leomanes/stargate/BOM/stargate_2.1.2.jpg

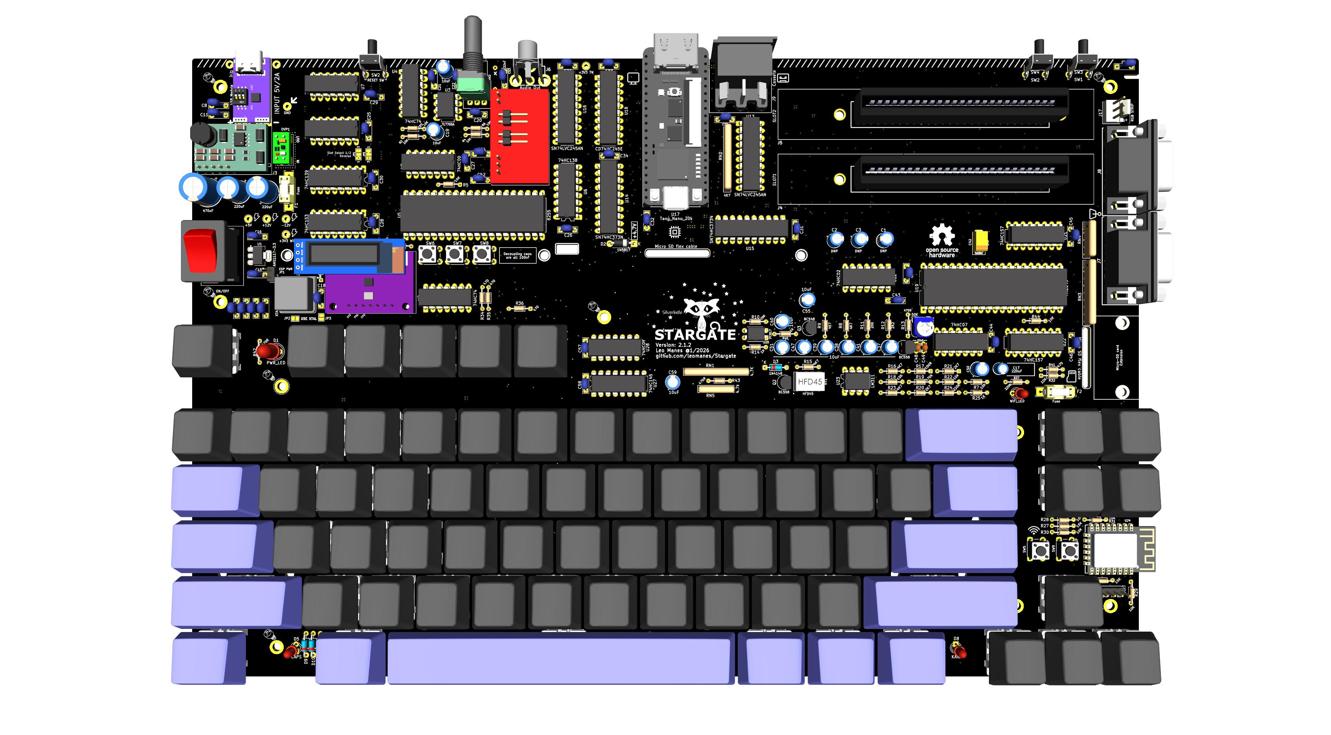
BOM/stargate_2.1.2.jpg
