leomanes/stargate/build/imgs/image009.png

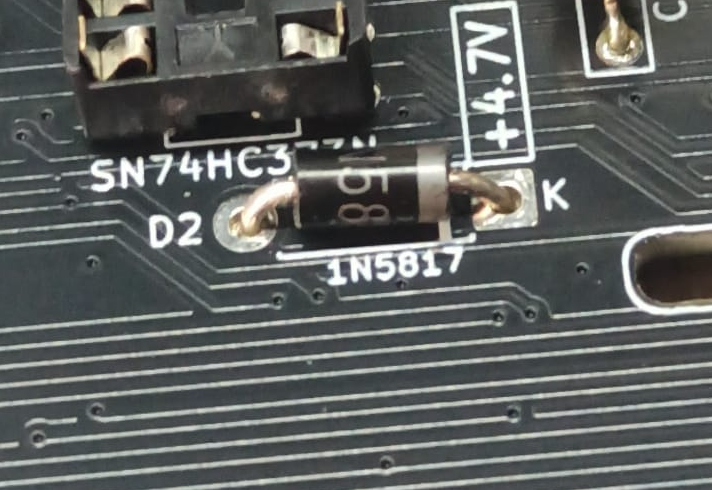
build/imgs/image009.png
