leomanes/stargate/kicad/version v2.1.3 production/Keyboard.kicad_sch

## KiCad design kicad/version v2.1.3 production/Keyboard.kicad_sch (2026-06-13)

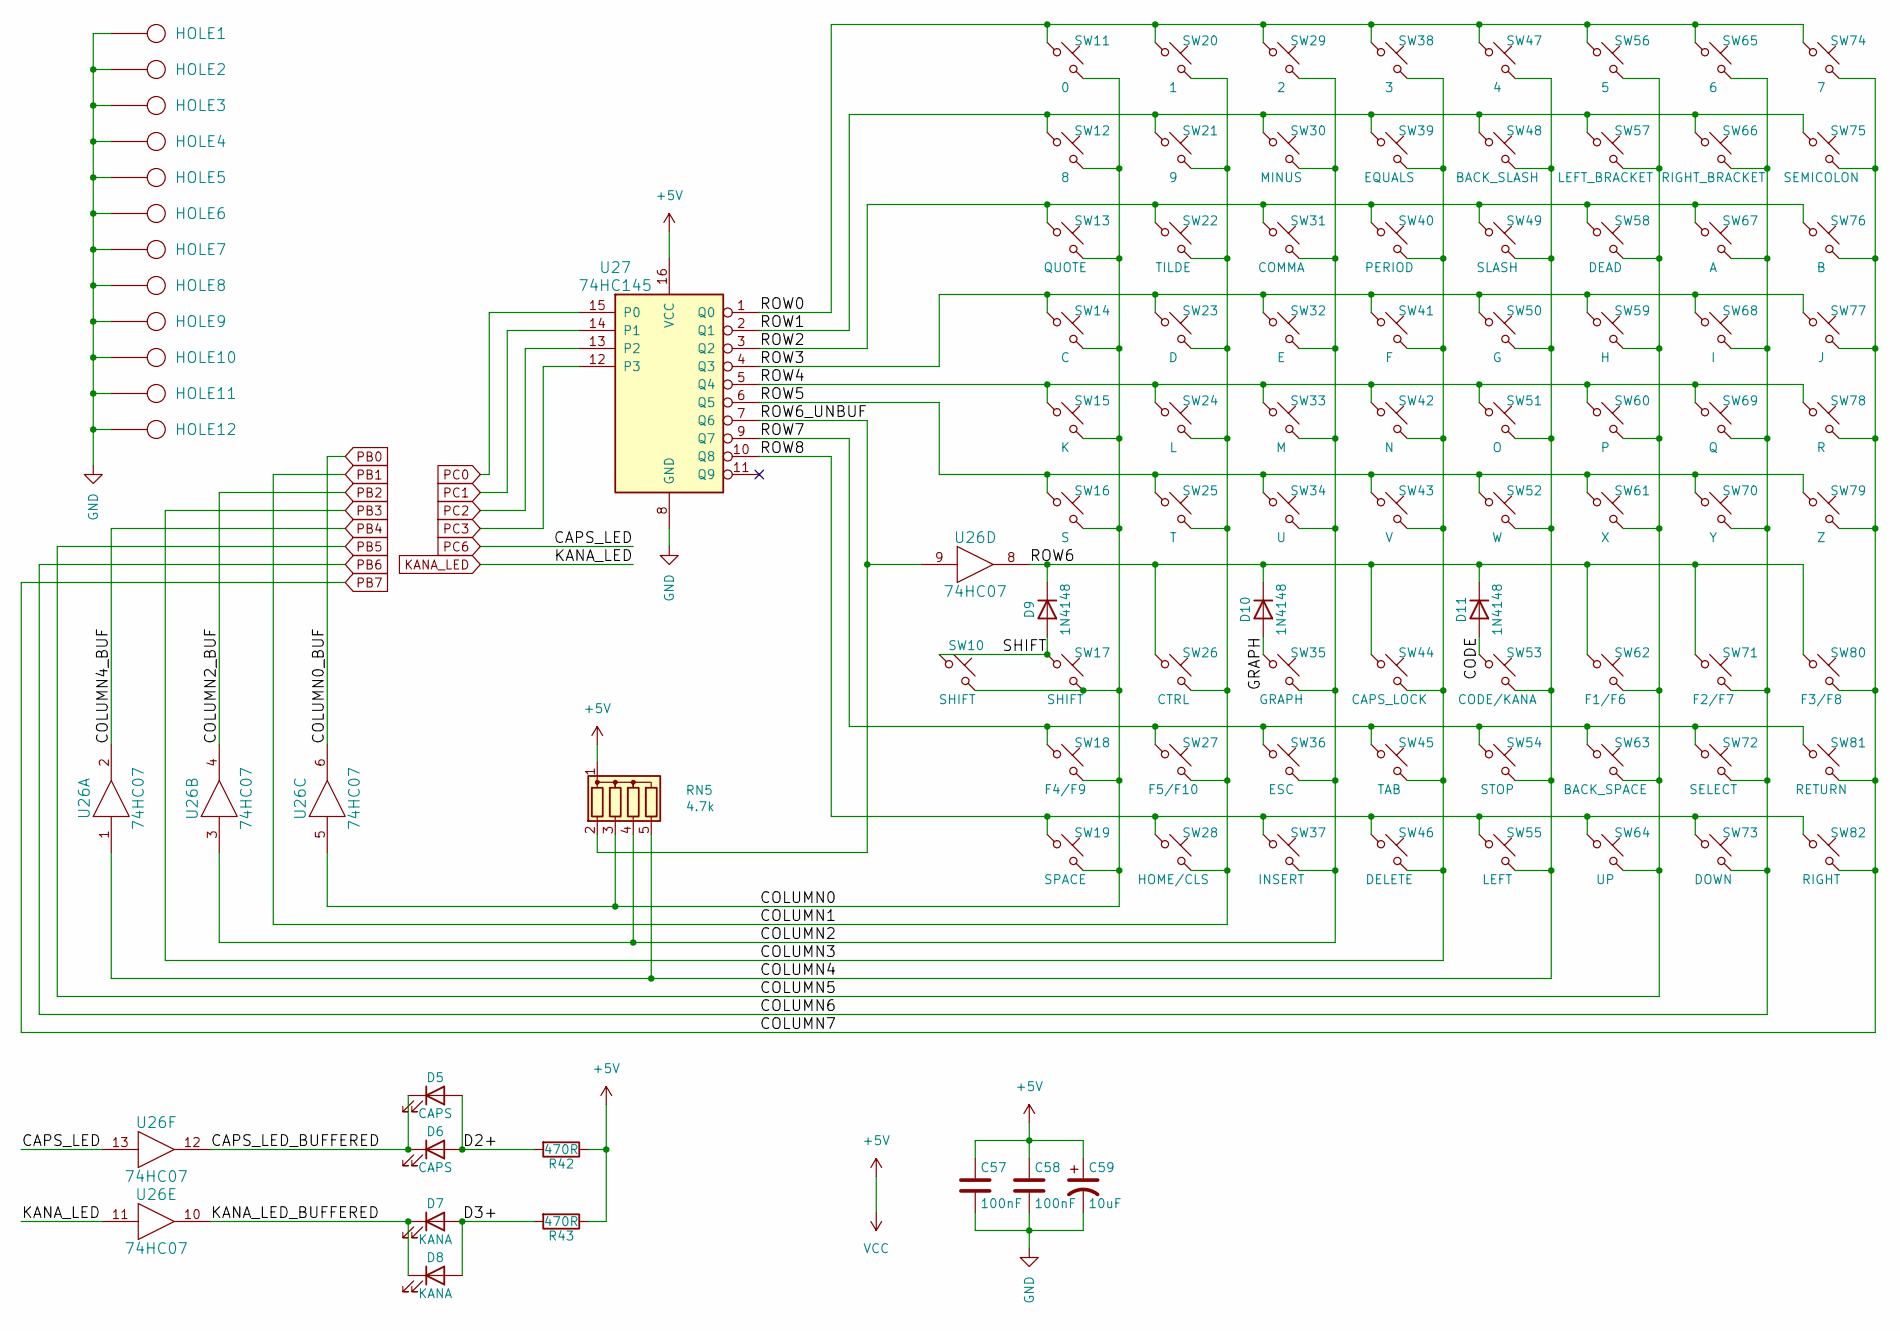
[picture p44: schematic Keyboard.kicad_sch]

Parts:
C57, C58: 100nF; CP_P5.00mm
C59: 10uF; CP_Radial_D5.0mm_P2.50mm
D5, D6: CAPS; LED_D3.0mm
D7, D8: KANA; LED_D3.0mm
D9, D10, D11: 1N4148; D_DO-35_SOD27_P7.62mm_Horizontal
HOLE1, HOLE2, HOLE3, HOLE4, HOLE5, HOLE6, HOLE7, HOLE8, HOLE9, HOLE12: HOLE; MountingHole_3mm_Pad_TopBottom_new
HOLE10, HOLE11: HOLE; MountingHole_2mm_Pad_TopBottom_new
R42, R43: 470R; R_Axial_DIN0204_L3.6mm_D1.6mm_P7.62mm_Horizontal
RN5: 4.7k; R_Array_SIP5
SW10: SHIFT; CHERRY_PCB_275H
SW11: 0; CHERRY_PCB_100H
SW12: 8; CHERRY_PCB_100H
SW13: QUOTE; CHERRY_PCB_100H
SW14: C; CHERRY_PCB_100H
SW15: K; CHERRY_PCB_100H
SW16: S; CHERRY_PCB_100H
SW17: SHIFT; CHERRY_PCB_225H
SW18: F4/F9; CHERRY_PCB_100H
SW19: SPACE; CHERRY_PCB_625H
SW20: 1; CHERRY_PCB_100H
SW21: 9; CHERRY_PCB_100H
SW22: TILDE; CHERRY_PCB_100H
SW23: D; CHERRY_PCB_100H
SW24: L; CHERRY_PCB_100H
SW25: T; CHERRY_PCB_100H
SW26: CTRL; CHERRY_PCB_125H
SW27: F5/F10; CHERRY_PCB_100H
SW28: HOME/CLS; CHERRY_PCB_100H
SW29: 2; CHERRY_PCB_100H
SW30: MINUS; CHERRY_PCB_100H
SW31: COMMA; CHERRY_PCB_100H
SW32: E; CHERRY_PCB_100H
SW33: M; CHERRY_PCB_100H
SW34: U; CHERRY_PCB_100H
SW35: GRAPH; CHERRY_PCB_125H
SW36: ESC; CHERRY_PCB_100H
SW37: INSERT; CHERRY_PCB_100H
SW38: 3; CHERRY_PCB_100H
SW39: EQUALS; CHERRY_PCB_100H
SW40: PERIOD; CHERRY_PCB_100H
SW41: F; CHERRY_PCB_100H
SW42: N; CHERRY_PCB_100H
SW43: V; CHERRY_PCB_100H
SW44: CAPS_LOCK; CHERRY_PCB_175H
SW45: TAB; CHERRY_PCB_150H
SW46: DELETE; CHERRY_PCB_100H
SW47: 4; CHERRY_PCB_100H
SW48: BACK_SLASH; CHERRY_PCB_150H
SW49: SLASH; CHERRY_PCB_100H
SW50: G; CHERRY_PCB_100H
SW51: O; CHERRY_PCB_100H
SW52: W; CHERRY_PCB_100H
SW53: CODE/KANA; CHERRY_PCB_125H
SW54: STOP; CHERRY_PCB_100H
SW55: LEFT; CHERRY_PCB_100H
SW56: 5; CHERRY_PCB_100H
SW57: LEFT_BRACKET; CHERRY_PCB_100H
SW58: DEAD; CHERRY_PCB_125H
SW59: H; CHERRY_PCB_100H
SW60: P; CHERRY_PCB_100H
SW61: X; CHERRY_PCB_100H
SW62: F1/F6; CHERRY_PCB_100H
SW63: BACK_SPACE; CHERRY_PCB_200H
SW64: UP; CHERRY_PCB_100H
SW65: 6; CHERRY_PCB_100H
SW66: RIGHT_BRACKET; CHERRY_PCB_100H
SW67: A; CHERRY_PCB_100H
SW68: I; CHERRY_PCB_100H
SW69: Q; CHERRY_PCB_100H
SW70: Y; CHERRY_PCB_100H
SW71: F2/F7; CHERRY_PCB_100H
SW72: SELECT; CHERRY_PCB_125H
SW73: DOWN; CHERRY_PCB_100H
SW74: 7; CHERRY_PCB_100H
SW75: SEMICOLON; CHERRY_PCB_100H
SW76: B; CHERRY_PCB_100H
SW77: J; CHERRY_PCB_100H
SW78: R; CHERRY_PCB_100H
SW79: Z; CHERRY_PCB_100H
SW80: F3/F8; CHERRY_PCB_100H
SW81: RETURN; CHERRY_PCB_225H
SW82: RIGHT; CHERRY_PCB_100H
U26: 74HC07; DIP-14_W7.62mm
U27: 74HC145; DIP-16_W7.62mm

Connections:
+5V: C57.1, C58.1, C59.1, R42.1, R43.1, RN5.1 (common), U27.16 (VCC)
CAPS_LED_BUFFERED: D5.1 (K), D6.1 (K), U26.12
CODE: D11.2 (A), SW53.1
COLUMN0: RN5.3 (R2), SW10.2, SW11.2, SW12.2, SW13.2, SW14.2, SW15.2, SW16.2, SW17.2, SW18.2, SW19.2, U26.5
COLUMN2: RN5.4 (R3), SW29.2, SW30.2, SW31.2, SW32.2, SW33.2, SW34.2, SW35.2, SW36.2, SW37.2, U26.3
COLUMN4: RN5.5 (R4), SW47.2, SW48.2, SW49.2, SW50.2, SW51.2, SW52.2, SW53.2, SW54.2, SW55.2, U26.1
D2+: D5.2 (A), D6.2 (A), R42.2
D3+: D7.2 (A), D8.2 (A), R43.2
GND: C57.2, C58.2, C59.2, HOLE1.1, HOLE2.1, HOLE3.1, HOLE4.1, HOLE5.1, HOLE6.1, HOLE7.1, HOLE8.1, HOLE9.1, HOLE10.1, HOLE11.1, HOLE12.1, U27.8 (GND)
GRAPH: D10.2 (A), SW35.1
KANA_LED: U26.11
KANA_LED_BUFFERED: D7.1 (K), D8.1 (K), U26.10
PB0: U26.6
PB1: SW20.2, SW21.2, SW22.2, SW23.2, SW24.2, SW25.2, SW26.2, SW27.2, SW28.2
PB2: U26.4
PB3: SW38.2, SW39.2, SW40.2, SW41.2, SW42.2, SW43.2, SW44.2, SW45.2, SW46.2
PB4: U26.2
PB5: SW56.2, SW57.2, SW58.2, SW59.2, SW60.2, SW61.2, SW62.2, SW63.2, SW64.2
PB6: SW65.2, SW66.2, SW67.2, SW68.2, SW69.2, SW70.2, SW71.2, SW72.2, SW73.2
PB7: SW74.2, SW75.2, SW76.2, SW77.2, SW78.2, SW79.2, SW80.2, SW81.2, SW82.2
PC0: U27.15 (P0)
PC1: U27.14 (P1)
PC2: U27.13 (P2)
PC3: U27.12 (P3)
PC6: U26.13
ROW0: SW11.1, SW20.1, SW29.1, SW38.1, SW47.1, SW56.1, SW65.1, SW74.1, U27.1 (Q0)
ROW1: SW12.1, SW21.1, SW30.1, SW39.1, SW48.1, SW57.1, SW66.1, SW75.1, U27.2 (Q1)
ROW2: SW13.1, SW22.1, SW31.1, SW40.1, SW49.1, SW58.1, SW67.1, SW76.1, U27.3 (Q2)
ROW3: SW14.1, SW23.1, SW32.1, SW41.1, SW50.1, SW59.1, SW68.1, SW77.1, U27.4 (Q3)
ROW4: SW15.1, SW24.1, SW33.1, SW42.1, SW51.1, SW60.1, SW69.1, SW78.1, U27.5 (Q4)
ROW5: SW16.1, SW25.1, SW34.1, SW43.1, SW52.1, SW61.1, SW70.1, SW79.1, U27.6 (Q5)
ROW6: D9.1 (K), D10.1 (K), D11.1 (K), SW26.1, SW44.1, SW62.1, SW71.1, SW80.1, U26.8
ROW6_UNBUF: RN5.2 (R1), U26.9, U27.7 (Q6)
ROW7: SW18.1, SW27.1, SW36.1, SW45.1, SW54.1, SW63.1, SW72.1, SW81.1, U27.9 (Q7)
ROW8: SW19.1, SW28.1, SW37.1, SW46.1, SW55.1, SW64.1, SW73.1, SW82.1, U27.10 (Q8)
SHIFT: D9.2 (A), SW10.1, SW17.1
