leomanes/stargate/kicad/version v2.1.3 production/RGBstrip.kicad_sch

## KiCad design kicad/version v2.1.3 production/RGBstrip.kicad_sch (2026-06-13)

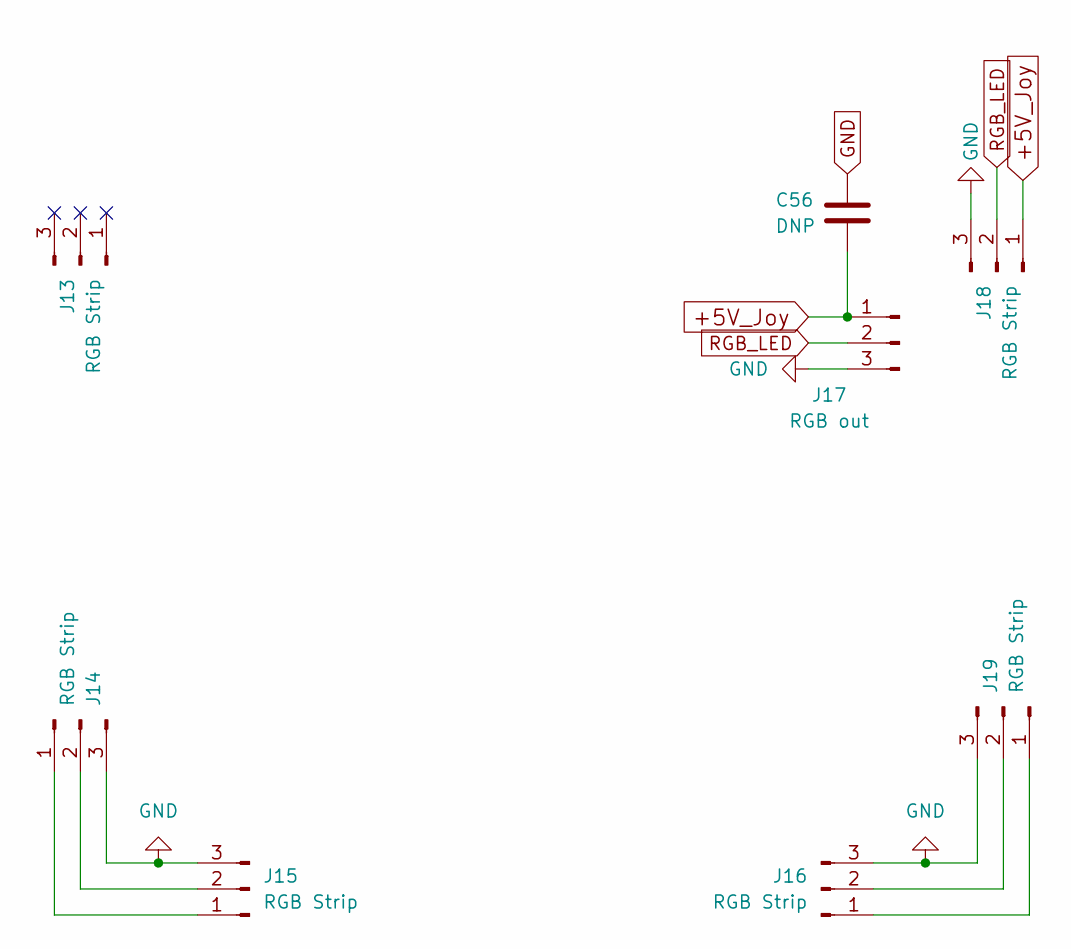
[picture p45: schematic RGBstrip.kicad_sch]

Parts:
C56: DNP; CP_P5.00mm; LCSC C14663
J13, J15, J19: RGB Strip; ledstrip_end
J14, J16, J18: RGB Strip; ledstrip
J17: RGB out; FanPinHeader_1x03_P2.54mm_Vertical

Connections:
+5V_Joy: C56.1, J17.1, J18.1
GND: C56.2, J14.3, J15.3, J16.3, J17.3, J18.3, J19.3
unnamed: J14.1, J15.1
unnamed: J14.2, J15.2
unnamed: J16.1, J19.1
unnamed: J16.2, J19.2
RGB_LED: J17.2, J18.2
