leomanes/stargate/kicad/version v2.1.3 production/amplifier.kicad_sch

## KiCad design kicad/version v2.1.3 production/amplifier.kicad_sch (2026-06-13)

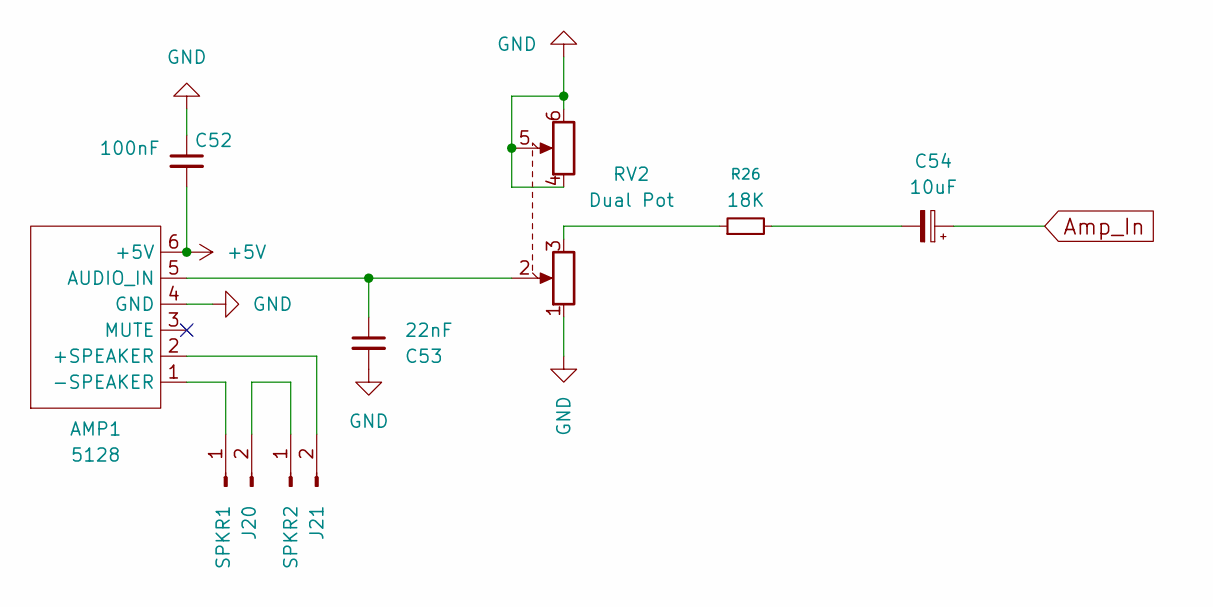
[picture p46: schematic amplifier.kicad_sch]

Parts:
AMP1: 5128; Amp5128
C52: 100nF; CP_P5.00mm
C53: 22nF; CP_P5.00mm
C54: 10uF; CP_Radial_D5.0mm_P2.50mm
J20: SPKR1; PinHeader_1x02_P2.54mm_Vertical
J21: SPKR2; PinHeader_1x02_P2.54mm_Vertical
R26: 18K; R_Axial_DIN0204_L3.6mm_D1.6mm_P7.62mm_Horizontal
RV2: Dual Pot; Potentiometer_Alps_RK097_Dual_Horizontal

Connections:
+5V: AMP1.6 (+5V), C52.2
Amp_In: C54.1
GND: AMP1.4 (GND), C52.1, C53.2, RV2.1, RV2.4, RV2.5, RV2.6
unnamed: AMP1.1 (-SPEAKER), J20.1
unnamed: AMP1.2 (+SPEAKER), J21.2
unnamed: AMP1.5 (AUDIO_IN), C53.1, RV2.2
unnamed: C54.2, R26.2
unnamed: J20.2, J21.1
unnamed: R26.1, RV2.3
