leomanes/stargate/kicad/version v2.1.3 production/bluetooth.kicad_sch

## KiCad design kicad/version v2.1.3 production/bluetooth.kicad_sch (2026-06-13)

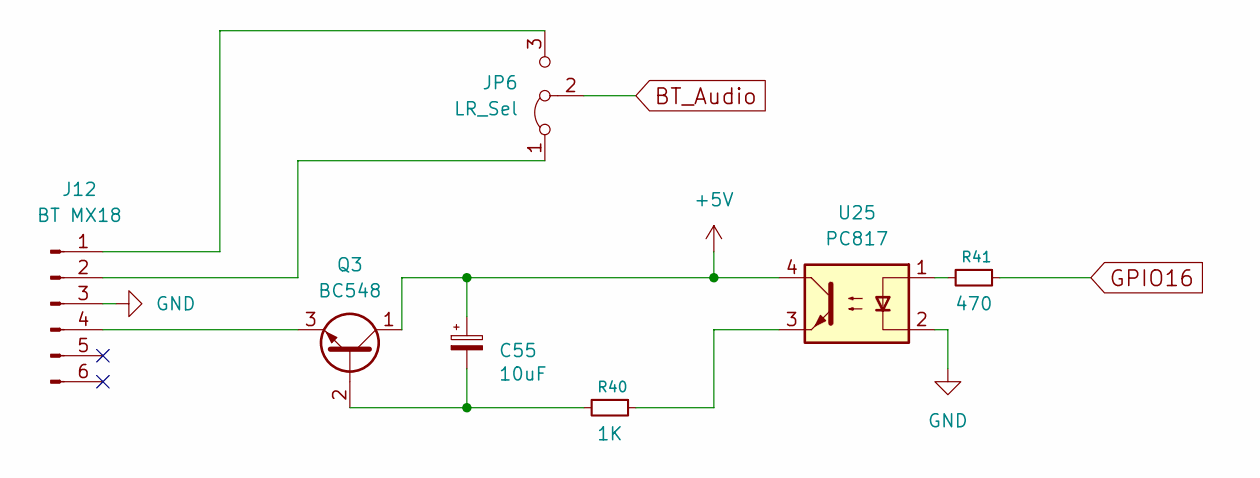
[picture p47: schematic bluetooth.kicad_sch]

Parts:
C55: 10uF; CP_Radial_D5.0mm_P2.50mm
J12: BT MX18; MH-M18
JP6: LR_Sel; SolderJumper-3_P1.3mm_Bridged12_Pad1.0x1.5mm_NumberLabels
Q3: BC548; TO-92
R40: 1K; R_Axial_DIN0204_L3.6mm_D1.6mm_P7.62mm_Horizontal
R41: 470; R_Axial_DIN0204_L3.6mm_D1.6mm_P7.62mm_Horizontal
U25: PC817; DIP-4_W7.62mm

Connections:
+5V: C55.1, Q3.1 (C), U25.4
BT_Audio: JP6.2 (C)
GND: J12.3, U25.2
GPIO16: R41.1
unnamed: C55.2, Q3.2 (B), R40.2
unnamed: J12.1, JP6.3 (B)
unnamed: J12.2, JP6.1 (A)
unnamed: J12.4, Q3.3 (E)
unnamed: R40.1, U25.3
unnamed: R41.2, U25.1
