leomanes/stargate/kicad/version v2.1.3 production/casette.kicad_sch

## KiCad design kicad/version v2.1.3 production/casette.kicad_sch (2026-06-13)

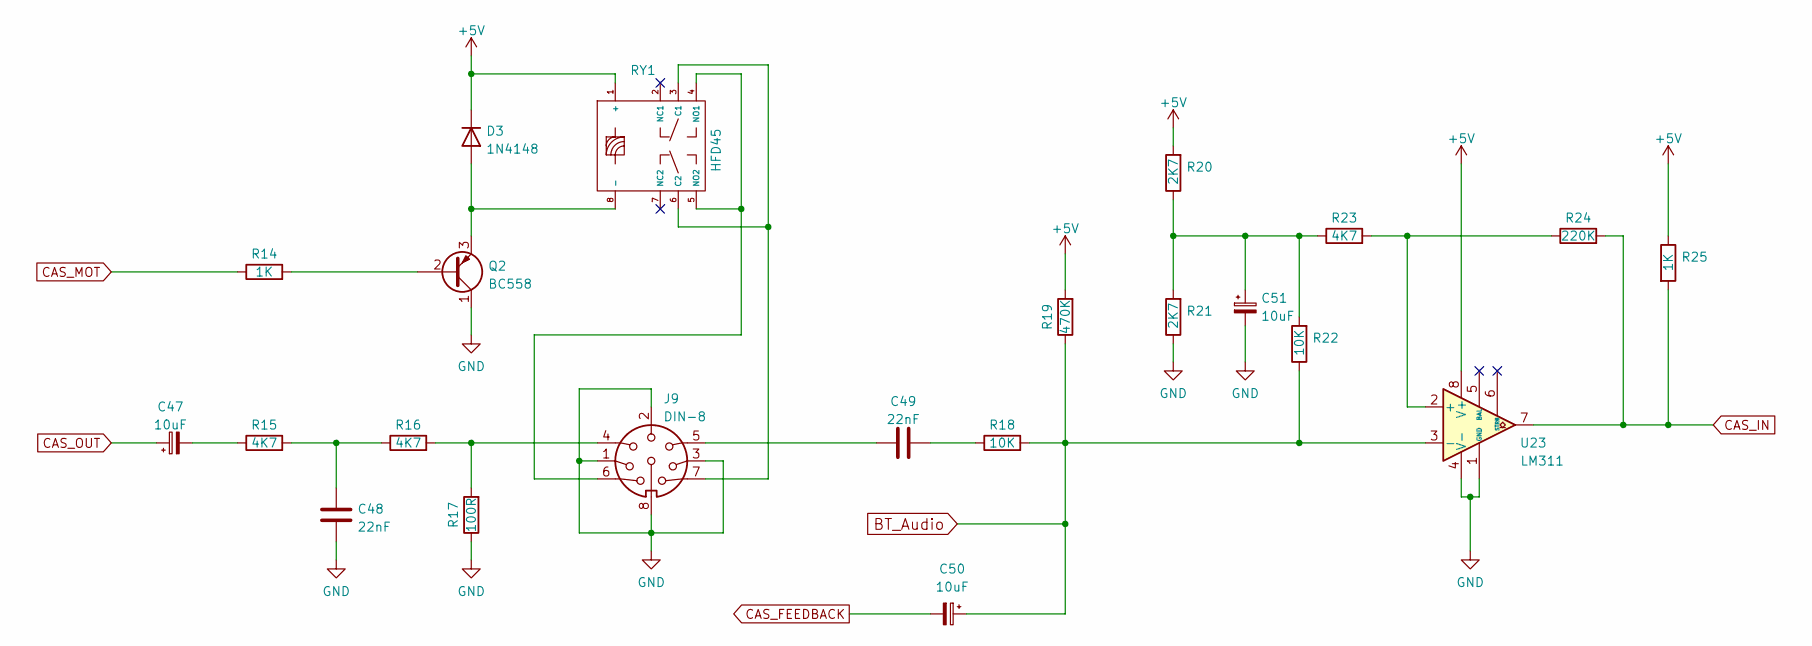
[picture p48: schematic casette.kicad_sch]

Parts:
C47, C50, C51: 10uF; CP_Radial_D5.0mm_P2.50mm
C48, C49: 22nF; C_Disc_D3.0mm_W2.0mm_P2.50mm
D3: 1N4148; D_DO-35_SOD27_P7.62mm_Horizontal
J9: DIN-8; DIN8
Q2: BC558; TO-92
R14, R25: 1K; R_Axial_DIN0204_L3.6mm_D1.6mm_P7.62mm_Horizontal
R15, R16, R23: 4K7; R_Axial_DIN0204_L3.6mm_D1.6mm_P7.62mm_Horizontal
R17: 100R; R_Axial_DIN0204_L3.6mm_D1.6mm_P7.62mm_Horizontal
R18, R22: 10K; R_Axial_DIN0204_L3.6mm_D1.6mm_P7.62mm_Horizontal
R19: 470K; R_Axial_DIN0204_L3.6mm_D1.6mm_P7.62mm_Horizontal
R20, R21: 2K7; R_Axial_DIN0204_L3.6mm_D1.6mm_P7.62mm_Horizontal
R24: 220K; R_Axial_DIN0204_L3.6mm_D1.6mm_P7.62mm_Horizontal
RY1: HFD45
U23: LM311; DIP-8_W7.62mm_LongPads

Connections:
+5V: D3.1 (K), R19.2, R20.2, R25.1, RY1.1 (+), U23.8 (V+)
BT_Audio: C50.1, R18.2, R19.1, R22.1, U23.3 (-)
CAS_FEEDBACK: C50.2
CAS_IN: R24.2, R25.2, U23.7
CAS_MOT: R14.1
CAS_OUT: C47.1
GND: C48.1, C51.2, J9.1, J9.2, J9.3, J9.8, Q2.1 (C), R17.1, R21.1, U23.1 (GND), U23.4 (V-)
unnamed: C47.2, R15.1
unnamed: C48.2, R15.2, R16.1
unnamed: C49.1, J9.5
unnamed: C49.2, R18.1
unnamed: C51.1, R20.1, R21.2, R22.2, R23.1
unnamed: D3.2 (A), Q2.3 (E), RY1.8 (-)
unnamed: J9.4, R16.2, R17.2
unnamed: J9.6, RY1.4 (NO1), RY1.5 (NO2)
unnamed: J9.7, RY1.3 (C1), RY1.6 (C2)
unnamed: Q2.2 (B), R14.2
unnamed: R23.2, R24.1, U23.2 (+)
