leomanes/stargate/kicad/version v2.1.3 production/clock.kicad_sch

## KiCad design kicad/version v2.1.3 production/clock.kicad_sch (2026-06-13)

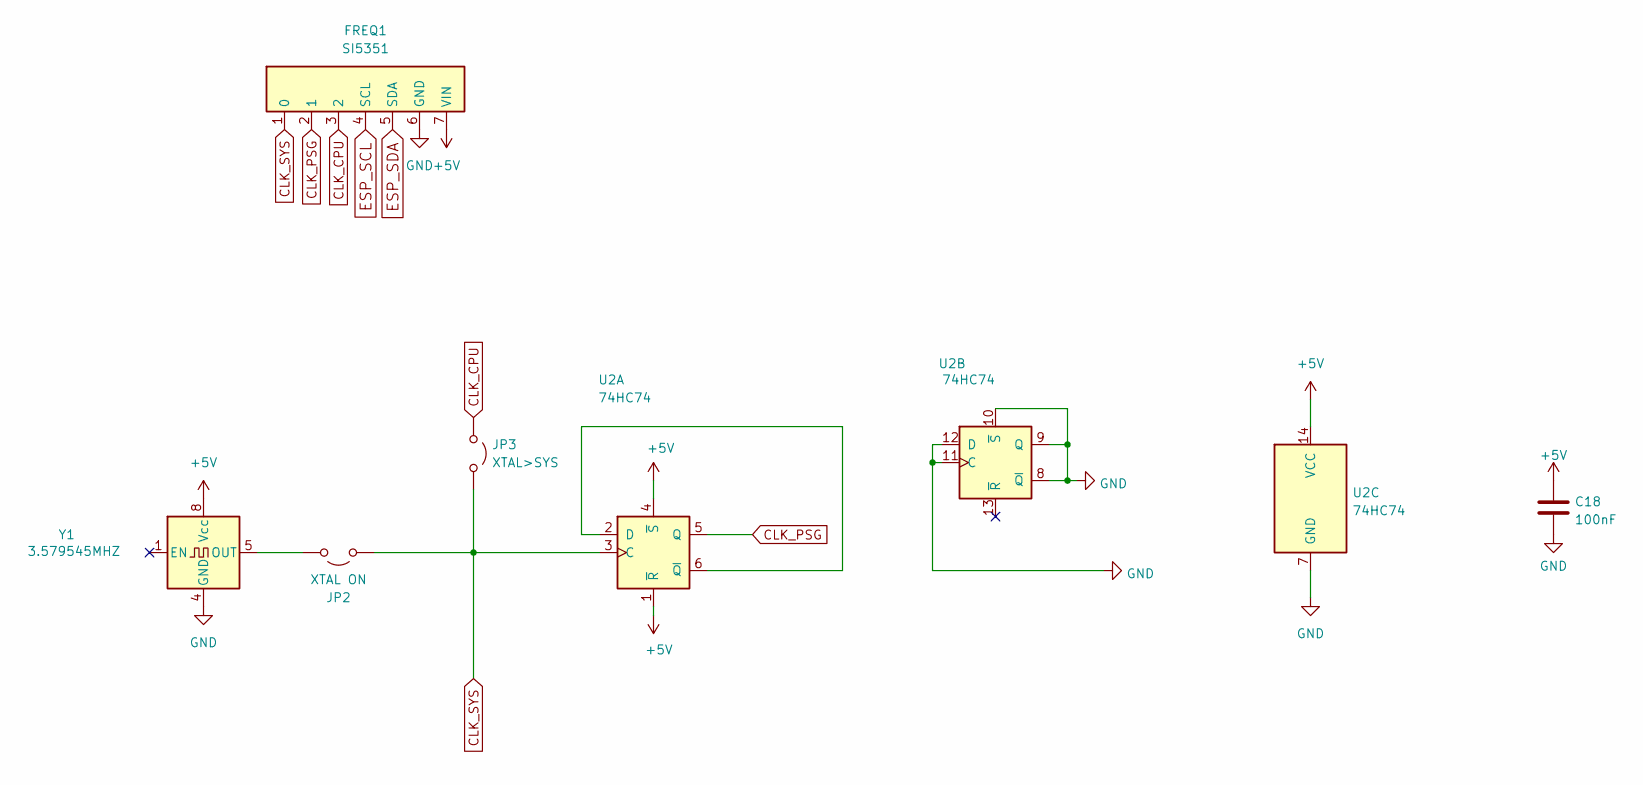
[picture p49: schematic clock.kicad_sch]

Parts:
C18: 100nF; CP_P5.00mm
FREQ1: SI5351; si5351
JP2: XTAL ON; SolderJumper-2_P1.3mm_Open_Pad1.0x1.5mm
JP3: XTAL>SYS; SolderJumper-2_P1.3mm_Open_Pad1.0x1.5mm
U2: 74HC74; DIP-14_W7.62mm_LongPads
Y1: 3.579545MHZ; Oscillator_DIP-8

Connections:
+5V: C18.1, FREQ1.7 (VIN), U2.1 (~R), U2.4 (~S), U2.14 (VCC), Y1.8 (Vcc)
CLK_CPU: FREQ1.3 (2), JP3.1 (A)
CLK_PSG: FREQ1.2 (1), U2.5 (Q)
CLK_SYS: FREQ1.1 (0), JP2.2 (B), JP3.2 (B), U2.3 (C)
ESP_SCL: FREQ1.4 (SCL)
ESP_SDA: FREQ1.5 (SDA)
GND: C18.2, FREQ1.6 (GND), U2.7 (GND), U2.8 (~Q), U2.9 (Q), U2.10 (~S), U2.11 (C), U2.12 (D), Y1.4 (GND)
unnamed: JP2.1 (A), Y1.5 (OUT)
unnamed: U2.2 (D), U2.6 (~Q)
