leomanes/stargate/kicad/version v2.1.3 production/cpu.kicad_sch

## KiCad design kicad/version v2.1.3 production/cpu.kicad_sch (2026-06-13)

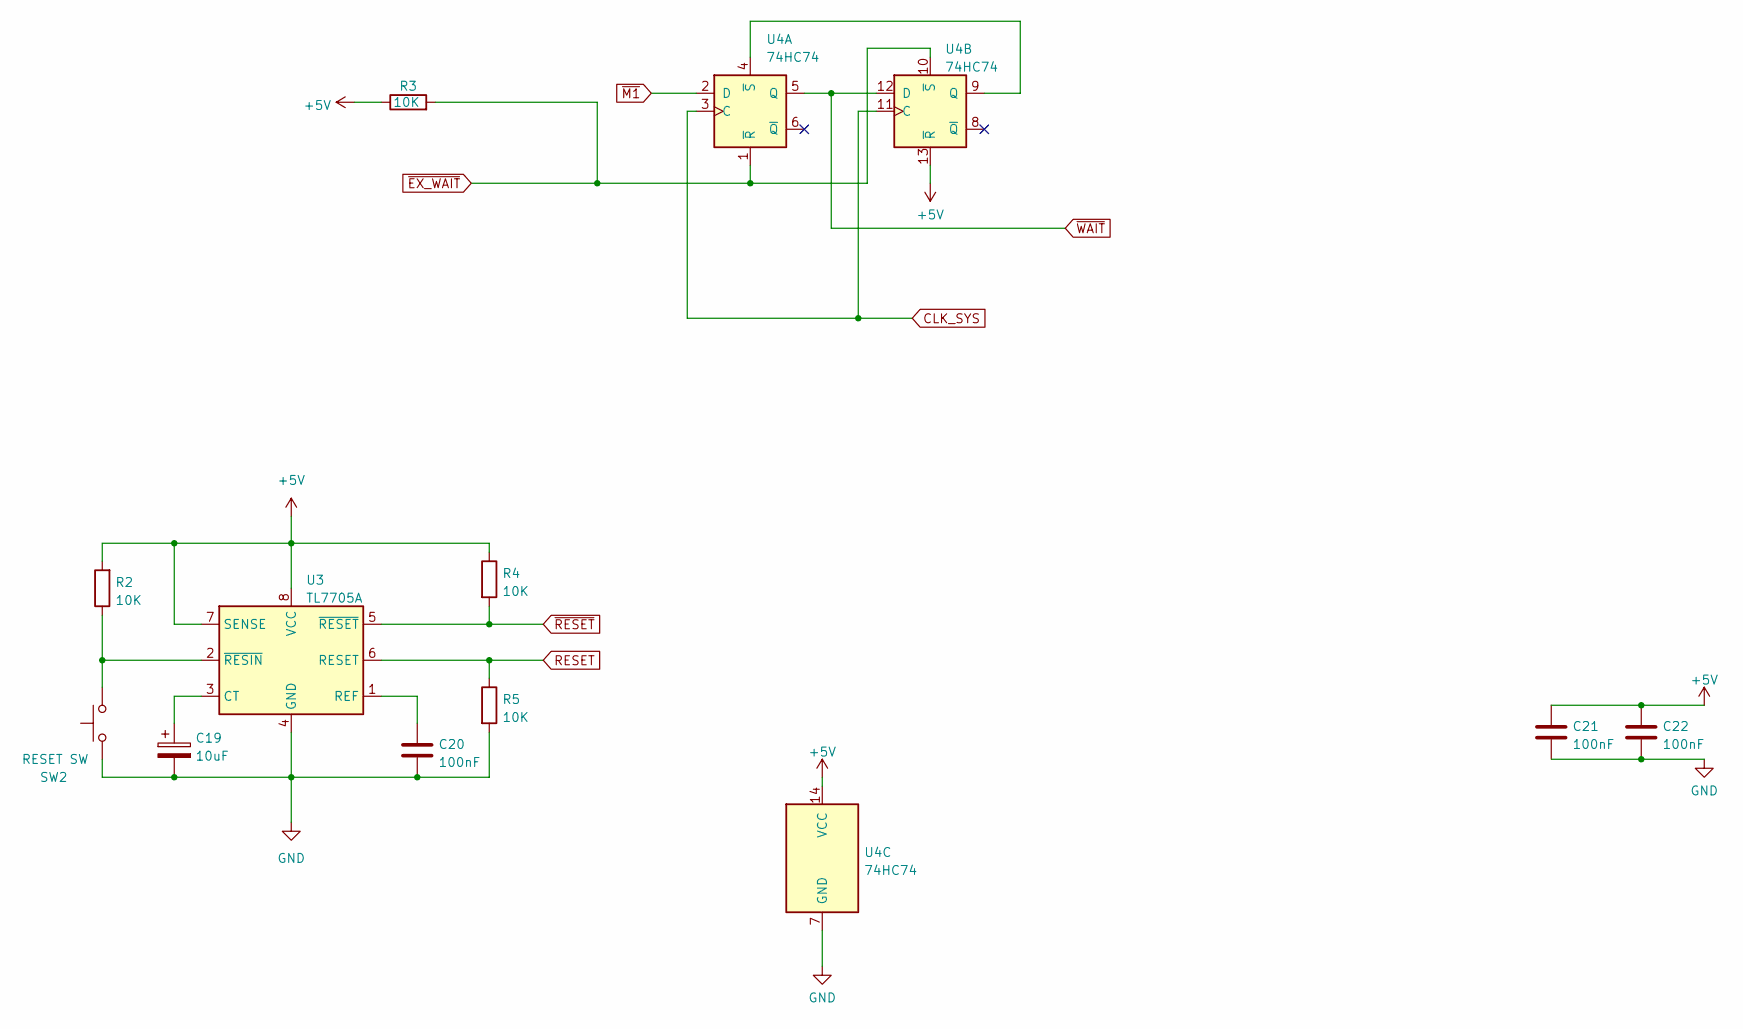
[picture p50: schematic cpu.kicad_sch]

Parts:
C19: 10uF; CP_Radial_D5.0mm_P2.50mm
C20, C21, C22: 100nF; CP_P5.00mm
R2, R3, R4, R5: 10K; R_Axial_DIN0204_L3.6mm_D1.6mm_P7.62mm_Horizontal
SW2: RESET SW; SW_Tactile_SPST_Angled_PTS645Vx83-2LFS
U3: TL7705A; DIP-8_W7.62mm_LongPads
U4: 74HC74; DIP-14_W7.62mm_LongPads

Connections:
+5V: C21.1, C22.1, R2.2, R3.1, R4.1, U3.7 (SENSE), U3.8 (VCC), U4.13 (~R), U4.14 (VCC)
CLK_SYS: U4.3 (C), U4.11 (C)
GND: C19.2, C20.2, C21.2, C22.2, R5.2, SW2.1, U3.4 (GND), U4.7 (GND)
unnamed: C19.1, U3.3 (CT)
unnamed: C20.1, U3.1 (REF)
unnamed: R2.1, SW2.2, U3.2 (~RESIN)
unnamed: U4.4 (~S), U4.9 (Q)
RESET: R5.1, U3.6 (RESET)
~EX_WAIT: R3.2, U4.1 (~R), U4.10 (~S)
~M1: U4.2 (D)
~RESET: R4.2, U3.5 (~RESET)
~WAIT: U4.5 (Q), U4.12 (D)
