leomanes/stargate/kicad/version v2.1.3 production/cpu_adapter.kicad_sch

## KiCad design kicad/version v2.1.3 production/cpu_adapter.kicad_sch (2026-06-13)

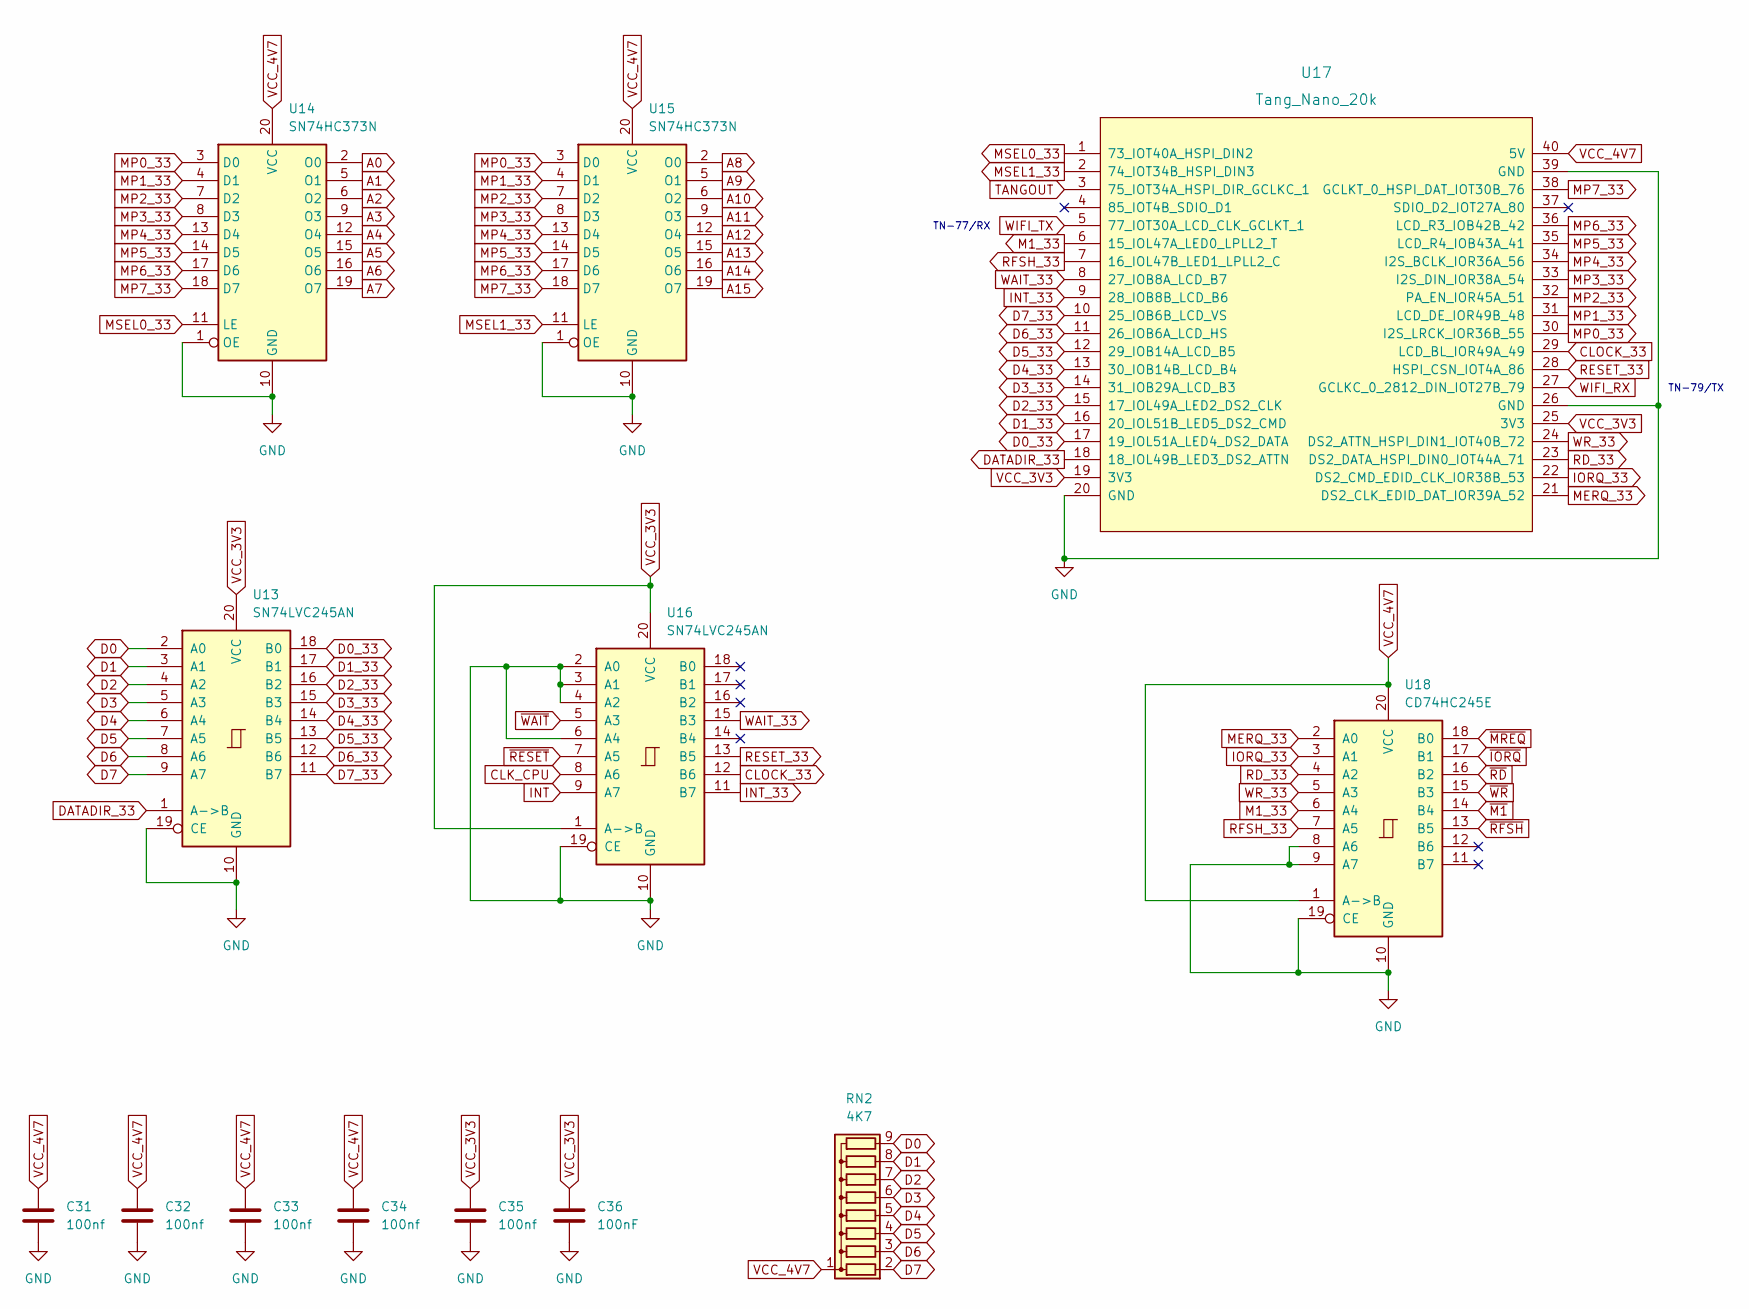
[picture p51: schematic cpu_adapter.kicad_sch]

Parts:
C31, C32, C33, C34, C35: 100nf; CP_P5.00mm
C36: 100nF; CP_P5.00mm
RN2: 4K7; R_Array_SIP9
U13, U16: SN74LVC245AN; DIP-20_W7.62mm_LongPads
U14, U15: SN74HC373N; DIP-20_W7.62mm_LongPads
U17: Tang_Nano_20k
U18: CD74HC245E; DIP-20_W7.62mm_LongPads

Connections:
A0: U14.2 (O0)
A1: U14.5 (O1)
A2: U14.6 (O2)
A3: U14.9 (O3)
A4: U14.12 (O4)
A5: U14.15 (O5)
A6: U14.16 (O6)
A7: U14.19 (O7)
A8: U15.2 (O0)
A9: U15.5 (O1)
A10: U15.6 (O2)
A11: U15.9 (O3)
A12: U15.12 (O4)
A13: U15.15 (O5)
A14: U15.16 (O6)
A15: U15.19 (O7)
CLK_CPU: U16.8 (A6)
CLOCK_33: U16.12 (B6), U17.29 (LCD_BL_IOR49A_49)
D0: RN2.9 (R8), U13.2 (A0)
D0_33: U13.18 (B0), U17.17 (19_IOL51A_LED4_DS2_DATA)
D1: RN2.8 (R7), U13.3 (A1)
D1_33: U13.17 (B1), U17.16 (20_IOL51B_LED5_DS2_CMD)
D2: RN2.7 (R6), U13.4 (A2)
D2_33: U13.16 (B2), U17.15 (17_IOL49A_LED2_DS2_CLK)
D3: RN2.6 (R5), U13.5 (A3)
D3_33: U13.15 (B3), U17.14 (31_IOB29A_LCD_B3)
D4: RN2.5 (R4), U13.6 (A4)
D4_33: U13.14 (B4), U17.13 (30_IOB14B_LCD_B4)
D5: RN2.4 (R3), U13.7 (A5)
D5_33: U13.13 (B5), U17.12 (29_IOB14A_LCD_B5)
D6: RN2.3 (R2), U13.8 (A6)
D6_33: U13.12 (B6), U17.11 (26_IOB6A_LCD_HS)
D7: RN2.2 (R1), U13.9 (A7)
D7_33: U13.11 (B7), U17.10 (25_IOB6B_LCD_VS)
DATADIR_33: U13.1 (A->B), U17.18 (18_IOL49B_LED3_DS2_ATTN)
GND: C31.2, C32.2, C33.2, C34.2, C35.2, C36.2, U13.10 (GND), U13.19 (CE), U14.1 (OE), U14.10 (GND), U15.1 (OE), U15.10 (GND), U16.2 (A0), U16.3 (A1), U16.4 (A2), U16.6 (A4), U16.10 (GND), U16.19 (CE), U17.20 (GND), U17.26 (GND), U17.39 (GND), U18.8 (A6), U18.9 (A7), U18.10 (GND), U18.19 (CE)
INT: U16.9 (A7)
INT_33: U16.11 (B7), U17.9 (28_IOB8B_LCD_B6)
IORQ_33: U17.22 (DS2_CMD_EDID_CLK_IOR38B_53), U18.3 (A1)
M1_33: U17.6 (15_IOL47A_LED0_LPLL2_T), U18.6 (A4)
MERQ_33: U17.21 (DS2_CLK_EDID_DAT_IOR39A_52), U18.2 (A0)
MP0_33: U14.3 (D0), U15.3 (D0), U17.30 (I2S_LRCK_IOR36B_55)
MP1_33: U14.4 (D1), U15.4 (D1), U17.31 (LCD_DE_IOR49B_48)
MP2_33: U14.7 (D2), U15.7 (D2), U17.32 (PA_EN_IOR45A_51)
MP3_33: U14.8 (D3), U15.8 (D3), U17.33 (I2S_DIN_IOR38A_54)
MP4_33: U14.13 (D4), U15.13 (D4), U17.34 (I2S_BCLK_IOR36A_56)
MP5_33: U14.14 (D5), U15.14 (D5), U17.35 (LCD_R4_IOB43A_41)
MP6_33: U14.17 (D6), U15.17 (D6), U17.36 (LCD_R3_IOB42B_42)
MP7_33: U14.18 (D7), U15.18 (D7), U17.38 (GCLKT_0_HSPI_DAT_IOT30B_76)
MSEL0_33: U14.11 (LE), U17.1 (73_IOT40A_HSPI_DIN2)
MSEL1_33: U15.11 (LE), U17.2 (74_IOT34B_HSPI_DIN3)
RD_33: U17.23 (DS2_DATA_HSPI_DIN0_IOT44A_71), U18.4 (A2)
RESET_33: U16.13 (B5), U17.28 (HSPI_CSN_IOT4A_86)
RFSH_33: U17.7 (16_IOL47B_LED1_LPLL2_C), U18.7 (A5)
TANGOUT: U17.3 (75_IOT34A_HSPI_DIR_GCLKC_1)
VCC_3V3: C35.1, C36.1, U13.20 (VCC), U16.1 (A->B), U16.20 (VCC), U17.19 (3V3), U17.25 (3V3)
VCC_4V7: C31.1, C32.1, C33.1, C34.1, RN2.1 (common), U14.20 (VCC), U15.20 (VCC), U17.40 (5V), U18.1 (A->B), U18.20 (VCC)
WAIT_33: U16.15 (B3), U17.8 (27_IOB8A_LCD_B7)
WIFI_RX: U17.27 (GCLKC_0_2812_DIN_IOT27B_79)
WIFI_TX: U17.5 (77_IOT30A_LCD_CLK_GCLKT_1)
WR_33: U17.24 (DS2_ATTN_HSPI_DIN1_IOT40B_72), U18.5 (A3)
~IORQ: U18.17 (B1)
~M1: U18.14 (B4)
~MREQ: U18.18 (B0)
~RD: U18.16 (B2)
~RESET: U16.7 (A5)
~RFSH: U18.13 (B5)
~WAIT: U16.5 (A3)
~WR: U18.15 (B3)

Notes on the sheet:
TN-77/RX
TN-79/TX
