leomanes/stargate/kicad/version v2.1.3 production/power.kicad_sch

## KiCad design kicad/version v2.1.3 production/power.kicad_sch (2026-06-13)

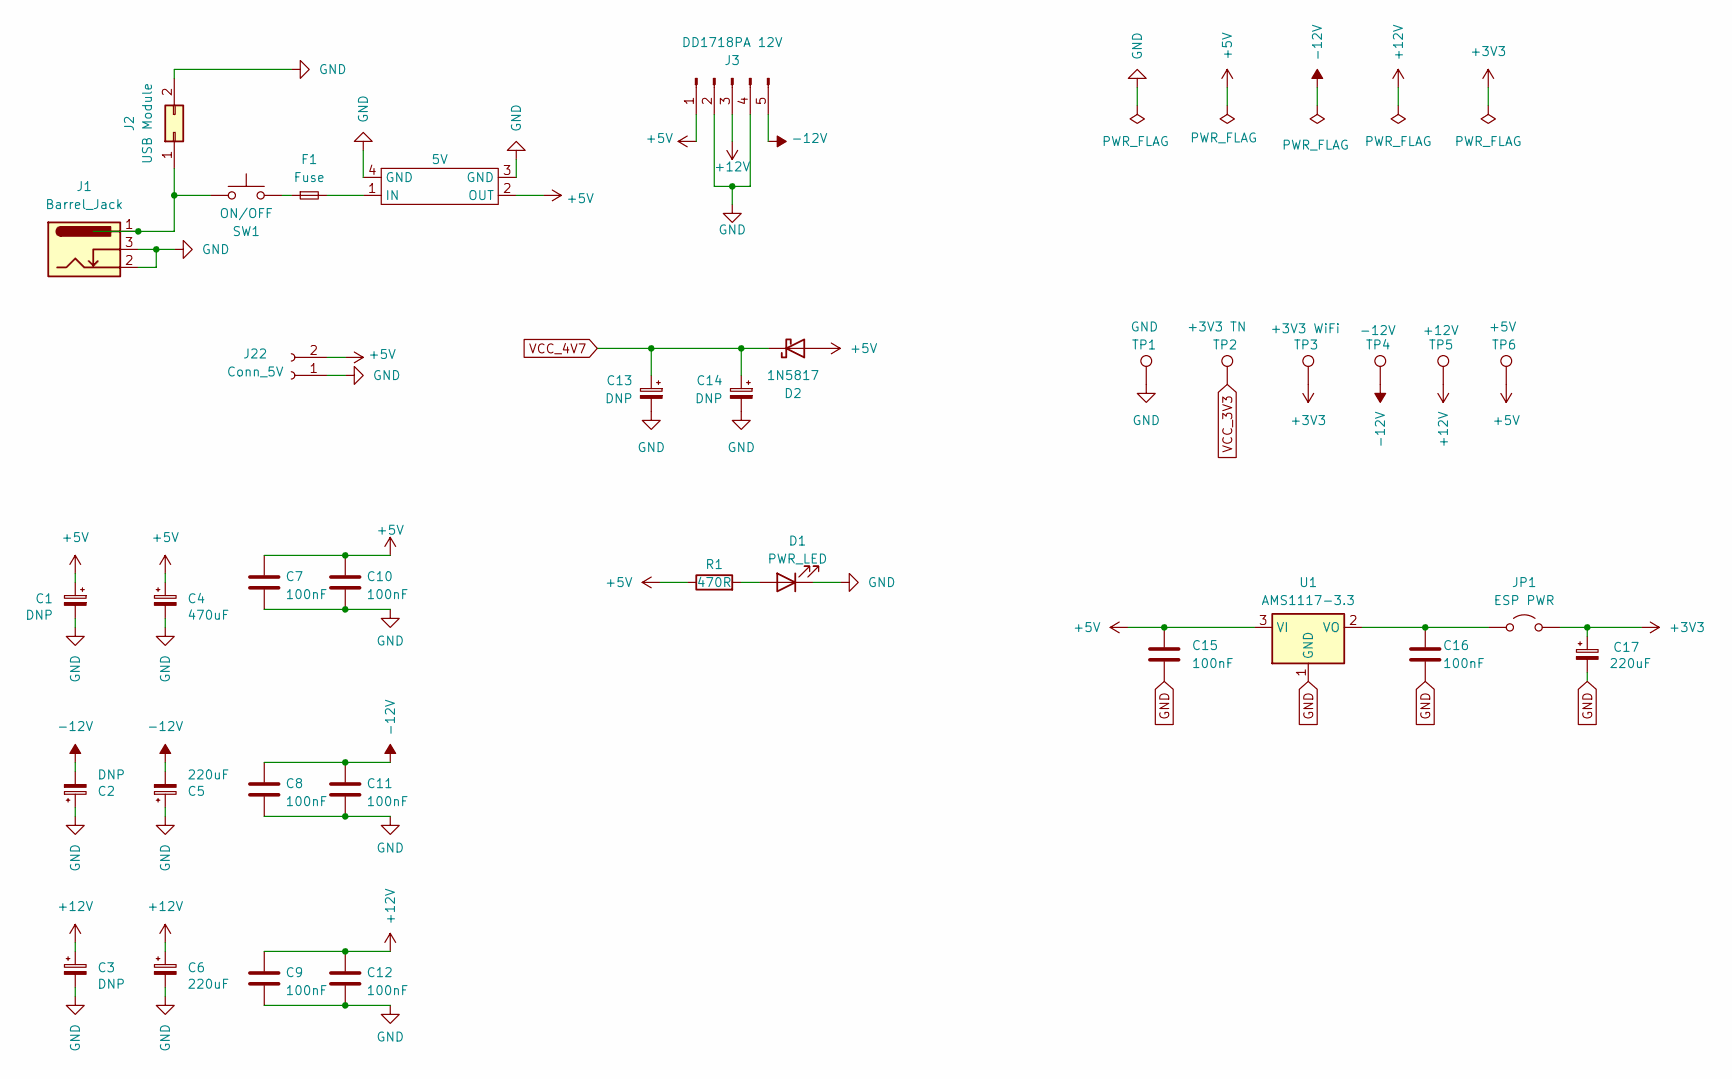
[picture p52: schematic power.kicad_sch]

Parts:
C1, C2, C3: DNP; CP_Radial_D5.0mm_P2.50mm
C4: 470uF; CP_Radial_D10.0mm_P5.00mm
C5, C6: 220uF; CP_Radial_D8.0mm_P3.50mm
C7, C8, C9, C10, C11, C12: 100nF; CP_P5.00mm
C13, C14: DNP; CP_EIA-7343-31_Kemet-D
C15, C16: 100nF; CP_P5.00mm; LCSC C14663
C17: 220uF; CP_Radial_D5.0mm_P2.50mm; LCSC C59461
D1: PWR_LED; LED_D5.0mm
D2: 1N5817; D_DO-41_SOD81_P7.62mm_Horizontal
F1: Fuse; THT+SMD(Fuse)
J1: Barrel_Jack; BarrelJack_Horizontal
J2: USB Module; USB-C Decoy
J3: DD1718PA 12V; dd1718pa_down
J22: Conn_5V; PinHeader_1x02_P2.54mm_Vertical
JP1: ESP PWR; PinHeader_1x02_P2.54mm_Vertical
OVP1: 5V; OVP
R1: 470R; R_Axial_DIN0204_L3.6mm_D1.6mm_P7.62mm_Horizontal
SW1: ON/OFF; SW_RF1-1A-DC-2-R-1
TP1: GND; TestPoint_THTPad_D2.5mm_Drill1.2mm
TP2: +3V3 TN; TestPoint_THTPad_D2.5mm_Drill1.2mm
TP3: +3V3 WiFi; TestPoint_THTPad_D2.5mm_Drill1.2mm
TP4: -12V; TestPoint_THTPad_D2.5mm_Drill1.2mm
TP5: +12V; TestPoint_THTPad_D2.5mm_Drill1.2mm
TP6: +5V; TestPoint_THTPad_D2.5mm_Drill1.2mm
U1: AMS1117-3.3; SOT-223-3_TabPin2

Connections:
+3V3: C17.1, JP1.2 (B), TP3.1
+5V: C1.1, C4.1, C7.1, C10.1, C15.1, D2.2 (A), J3.1, J22.2, OVP1.2 (OUT), R1.1, TP6.1, U1.3 (VI)
+12V: C3.1, C6.1, C9.1, C12.1, J3.3, TP5.1
-12V: C2.2, C5.2, C8.1, C11.1, J3.5, TP4.1
GND: C1.2, C2.1, C3.2, C4.2, C5.1, C6.2, C7.2, C8.2, C9.2, C10.2, C11.2, C12.2, C13.2, C14.2, C15.2, C16.2, C17.2, D1.1 (K), J1.2, J1.3, J2.2, J3.2, J3.4, J22.1, OVP1.3 (GND), OVP1.4 (GND), TP1.1, U1.1 (GND)
unnamed: C16.1, JP1.1 (A), U1.2 (VO)
unnamed: D1.2 (A), R1.2
unnamed: F1.1, SW1.2
unnamed: F1.2, OVP1.1 (IN)
unnamed: J1.1, J2.1, SW1.1
VCC_3V3: TP2.1
VCC_4V7: C13.1, C14.1, D2.1 (K)
