leomanes/stargate/kicad/version v2.1.3 production/ppi.kicad_sch

## KiCad design kicad/version v2.1.3 production/ppi.kicad_sch (2026-06-13)

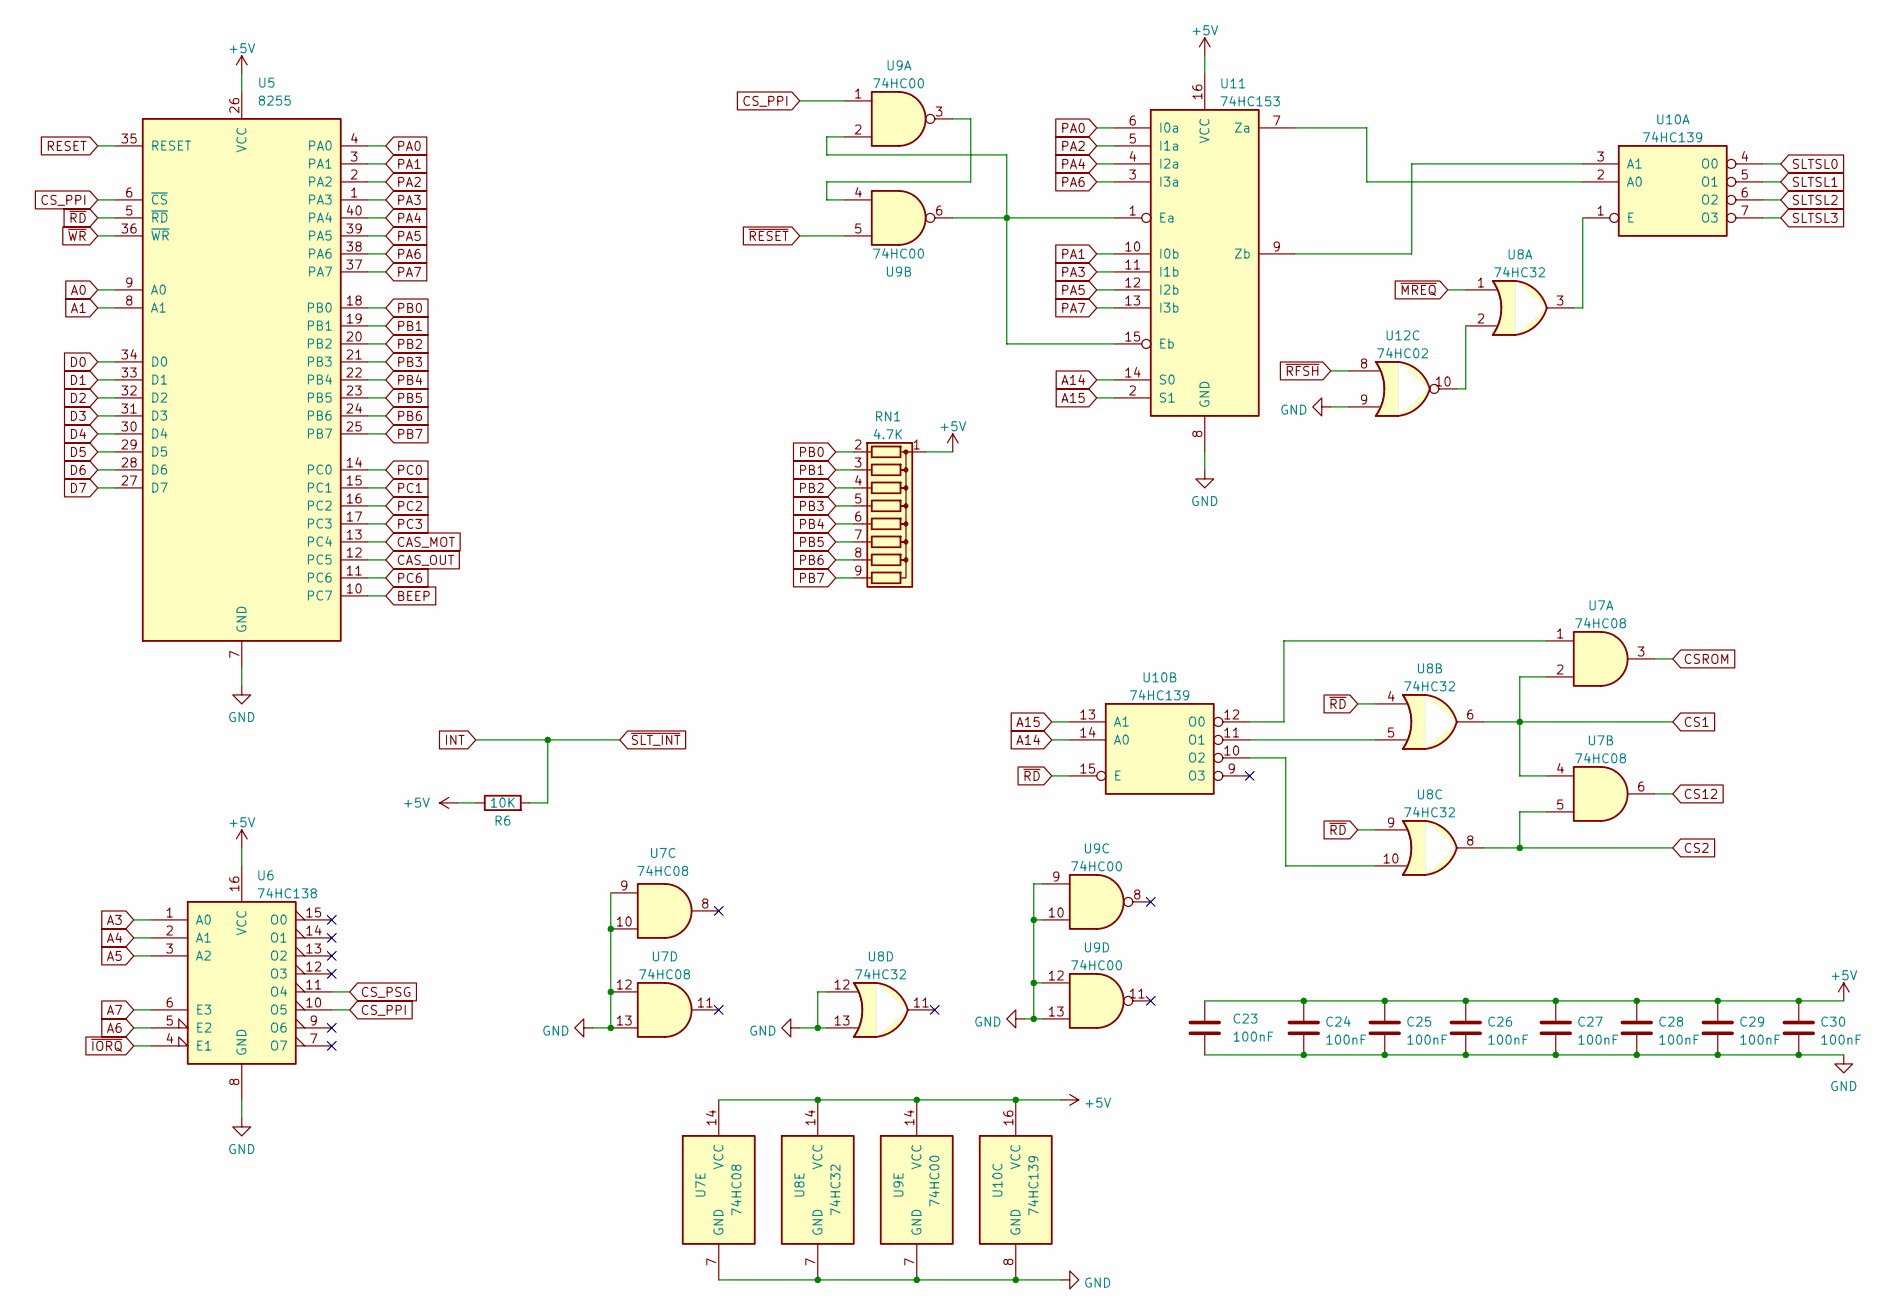
[picture p53: schematic ppi.kicad_sch]

Parts:
C23, C24, C25, C26, C27, C28, C29, C30: 100nF; CP_P5.00mm
R6: 10K; R_Axial_DIN0204_L3.6mm_D1.6mm_P7.62mm_Horizontal
RN1: 4.7K; R_Array_SIP9
U5: 8255; DIP-40_W15.24mm_LongPads
U6: 74HC138; DIP-16_W7.62mm_LongPads
U7: 74HC08; DIP-14_W7.62mm_LongPads
U8: 74HC32; DIP-14_W7.62mm_LongPads
U9: 74HC00; DIP-14_W7.62mm_LongPads
U10: 74HC139; DIP-16_W7.62mm_LongPads
U11: 74HC153; DIP-16_W7.62mm_LongPads
U12: 74HC02; DIP-14_W7.62mm_LongPads

Connections:
+5V: C23.1, C24.1, C25.1, C26.1, C27.1, C28.1, C29.1, C30.1, R6.1, RN1.1 (common), U5.26 (VCC), U6.16 (VCC), U7.14 (VCC), U8.14 (VCC), U9.14 (VCC), U10.16 (VCC), U11.16 (VCC)
A0: U5.9 (A0)
A1: U5.8 (A1)
A3: U6.1 (A0)
A4: U6.2 (A1)
A5: U6.3 (A2)
A6: U6.5 (E2)
A7: U6.6 (E3)
A14: U10.14 (A0), U11.14 (S0)
A15: U10.13 (A1), U11.2 (S1)
BEEP: U5.10 (PC7)
CAS_MOT: U5.13 (PC4)
CAS_OUT: U5.12 (PC5)
CS1: U7.2, U7.4, U8.6
CS2: U7.5, U8.8
CS12: U7.6
CSROM: U7.3
CS_PPI: U5.6 (~CS), U6.10 (O5), U9.1
CS_PSG: U6.11 (O4)
D0: U5.34 (D0)
D1: U5.33 (D1)
D2: U5.32 (D2)
D3: U5.31 (D3)
D4: U5.30 (D4)
D5: U5.29 (D5)
D6: U5.28 (D6)
D7: U5.27 (D7)
GND: C23.2, C24.2, C25.2, C26.2, C27.2, C28.2, C29.2, C30.2, U5.7 (GND), U6.8 (GND), U7.7 (GND), U7.9, U7.10, U7.12, U7.13, U8.7 (GND), U8.12, U8.13, U9.7 (GND), U9.9, U9.10, U9.12, U9.13, U10.8 (GND), U11.8 (GND), U12.9
INT: R6.2
unnamed: U9.3, U9.4
unnamed: U8.3, U10.1 (E)
unnamed: U10.2 (A0), U11.7 (Za)
unnamed: U10.3 (A1), U11.9 (Zb)
unnamed: U8.10, U10.10 (O2)
unnamed: U8.5, U10.11 (O1)
unnamed: U7.1, U10.12 (O0)
unnamed: U9.2, U9.6, U11.1 (Ea), U11.15 (Eb)
unnamed: U8.2, U12.10
PA0: U5.4 (PA0), U11.6 (I0a)
PA1: U5.3 (PA1), U11.10 (I0b)
PA2: U5.2 (PA2), U11.5 (I1a)
PA3: U5.1 (PA3), U11.11 (I1b)
PA4: U5.40 (PA4), U11.4 (I2a)
PA5: U5.39 (PA5), U11.12 (I2b)
PA6: U5.38 (PA6), U11.3 (I3a)
PA7: U5.37 (PA7), U11.13 (I3b)
PB0: RN1.2 (R1), U5.18 (PB0)
PB1: RN1.3 (R2), U5.19 (PB1)
PB2: RN1.4 (R3), U5.20 (PB2)
PB3: RN1.5 (R4), U5.21 (PB3)
PB4: RN1.6 (R5), U5.22 (PB4)
PB5: RN1.7 (R6), U5.23 (PB5)
PB6: RN1.8 (R7), U5.24 (PB6)
PB7: RN1.9 (R8), U5.25 (PB7)
PC0: U5.14 (PC0)
PC1: U5.15 (PC1)
PC2: U5.16 (PC2)
PC3: U5.17 (PC3)
PC6: U5.11 (PC6)
RESET: U5.35 (RESET)
SLTSL0: U10.4 (O0)
SLTSL1: U10.5 (O1)
SLTSL2: U10.6 (O2)
SLTSL3: U10.7 (O3)
~IORQ: U6.4 (E1)
~MREQ: U8.1
~RD: U5.5 (~RD), U8.4, U8.9, U10.15 (E)
~RESET: U9.5
~RFSH: U12.8
~WR: U5.36 (~WR)
