leomanes/stargate/kicad/version v2.1.3 production/psg.kicad_sch

## KiCad design kicad/version v2.1.3 production/psg.kicad_sch (2026-06-13)

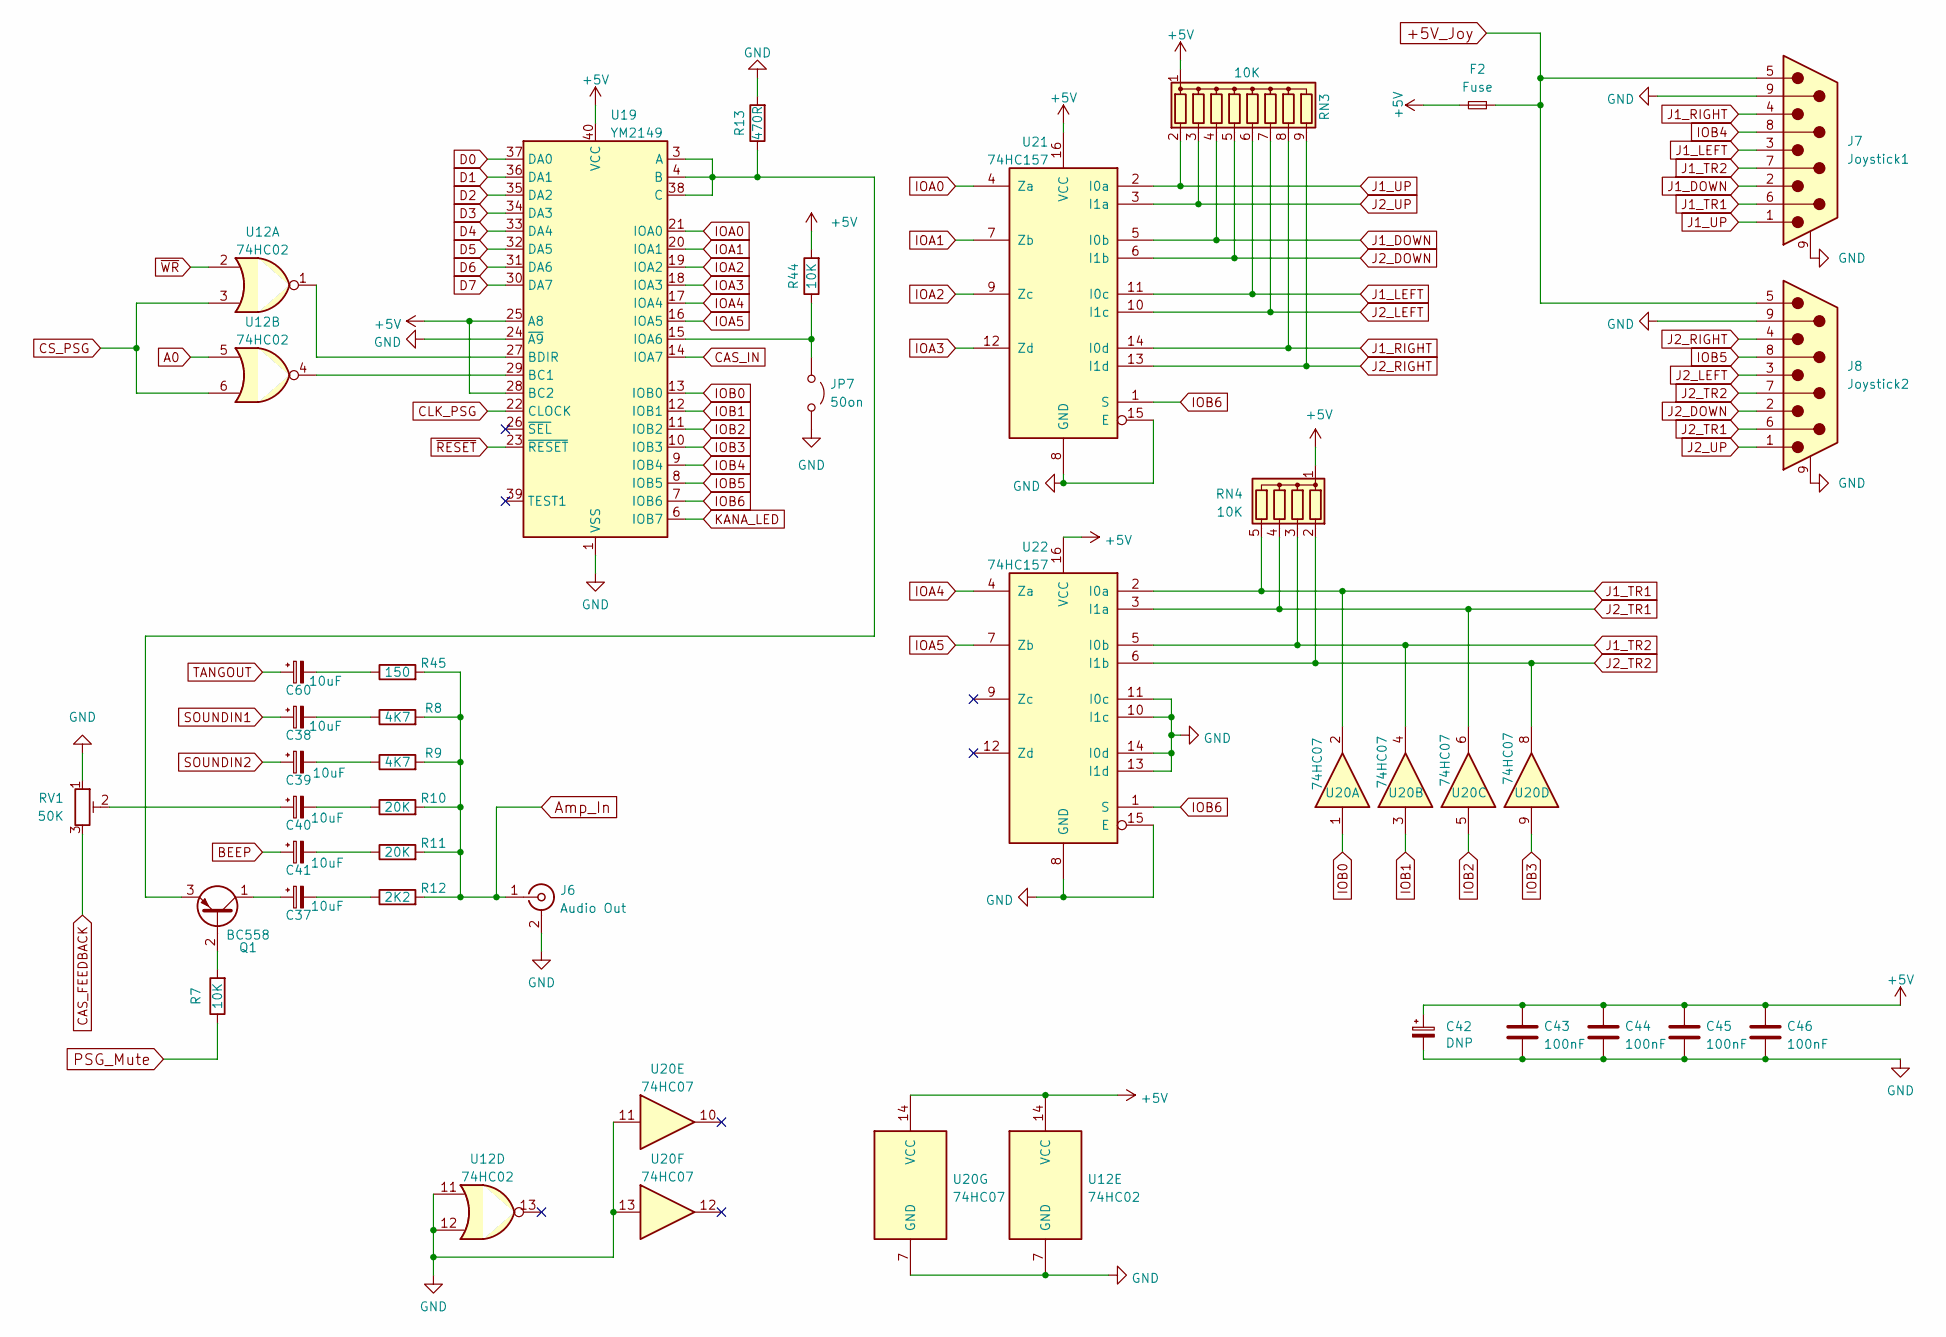
[picture p54: schematic psg.kicad_sch]

Parts:
C37, C38, C39, C40, C41, C60: 10uF; CP_Radial_D5.0mm_P2.50mm
C42: DNP; CP_EIA-7343-31_Kemet-D
C43, C44, C45, C46: 100nF; CP_P5.00mm
F2: Fuse; THT+SMD(Fuse)
J6: Audio Out; Conn_RCA_Right
J7: Joystick1; Conn_Dsub_DE9M
J8: Joystick2; Conn_Dsub_DE9M
JP7: 50on; SolderJumper-2_P1.3mm_Open_Pad1.0x1.5mm
Q1: BC558; TO-92
R7, R44: 10K; R_Axial_DIN0204_L3.6mm_D1.6mm_P7.62mm_Horizontal
R8, R9: 4K7; R_Axial_DIN0204_L3.6mm_D1.6mm_P7.62mm_Horizontal
R10, R11: 20K; R_Axial_DIN0204_L3.6mm_D1.6mm_P7.62mm_Horizontal
R12: 2K2; R_Axial_DIN0204_L3.6mm_D1.6mm_P7.62mm_Horizontal
R13: 470R; R_Axial_DIN0204_L3.6mm_D1.6mm_P7.62mm_Horizontal
R45: 150; R_Axial_DIN0204_L3.6mm_D1.6mm_P7.62mm_Horizontal
RN3: 10K; R_Array_SIP9
RN4: 10K; R_Array_SIP5
RV1: 50K; TrimPotLargeHole
U12: 74HC02; DIP-14_W7.62mm_LongPads
U19: YM2149; DIP-40_W15.24mm_LongPads
U20: 74HC07; DIP-14_W7.62mm_LongPads
U21, U22: 74HC157; DIP-16_W7.62mm_LongPads

Connections:
+5V: C42.1, C43.1, C44.1, C45.1, C46.1, F2.1, R44.2, RN3.1 (common), RN4.1 (common), U12.14 (VCC), U19.25 (A8), U19.28 (BC2), U19.40 (VCC), U20.14 (VCC), U21.16 (VCC), U22.16 (VCC)
+5V_Joy: F2.2, J7.5, J8.5
A0: U12.5
Amp_In: J6.1 (In), R8.2, R9.2, R10.2, R11.2, R12.2, R45.2
BEEP: C41.1
CAS_FEEDBACK: RV1.3
CAS_IN: U19.14 (IOA7)
CLK_PSG: U19.22 (CLOCK)
CS_PSG: U12.3, U12.6
D0: U19.37 (DA0)
D1: U19.36 (DA1)
D2: U19.35 (DA2)
D3: U19.34 (DA3)
D4: U19.33 (DA4)
D5: U19.32 (DA5)
D6: U19.31 (DA6)
D7: U19.30 (DA7)
GND: C42.2, C43.2, C44.2, C45.2, C46.2, J6.2 (Ext), J7.9, J8.9, JP7.2 (B), R13.2, RV1.1, U12.7 (GND), U12.11, U12.12, U19.1 (VSS), U19.24 (~A9), U20.7 (GND), U20.11, U20.13, U21.8 (GND), U21.15 (E), U22.8 (GND), U22.10 (I1c), U22.11 (I0c), U22.13 (I1d), U22.14 (I0d), U22.15 (E)
IOA0: U19.21 (IOA0), U21.4 (Za)
IOA1: U19.20 (IOA1), U21.7 (Zb)
IOA2: U19.19 (IOA2), U21.9 (Zc)
IOA3: U19.18 (IOA3), U21.12 (Zd)
IOA4: U19.17 (IOA4), U22.4 (Za)
IOA5: U19.16 (IOA5), U22.7 (Zb)
IOB0: U19.13 (IOB0), U20.1
IOB1: U19.12 (IOB1), U20.3
IOB2: U19.11 (IOB2), U20.5
IOB3: U19.10 (IOB3), U20.9
IOB4: J7.8, U19.9 (IOB4)
IOB5: J8.8, U19.8 (IOB5)
IOB6: U19.7 (IOB6), U21.1 (S), U22.1 (S)
J1_DOWN: J7.2, RN3.4 (R3), U21.5 (I0b)
J1_LEFT: J7.3, RN3.6 (R5), U21.11 (I0c)
J1_RIGHT: J7.4, RN3.8 (R7), U21.14 (I0d)
J1_TR1: J7.6, RN4.5 (R4), U20.2, U22.2 (I0a)
J1_TR2: J7.7, RN4.3 (R2), U20.4, U22.5 (I0b)
J1_UP: J7.1, RN3.2 (R1), U21.2 (I0a)
J2_DOWN: J8.2, RN3.5 (R4), U21.6 (I1b)
J2_LEFT: J8.3, RN3.7 (R6), U21.10 (I1c)
J2_RIGHT: J8.4, RN3.9 (R8), U21.13 (I1d)
J2_TR1: J8.6, RN4.4 (R3), U20.6, U22.3 (I1a)
J2_TR2: J8.7, RN4.2 (R1), U20.8, U22.6 (I1b)
J2_UP: J8.1, RN3.3 (R2), U21.3 (I1a)
KANA_LED: U19.6 (IOB7)
unnamed: C37.1, Q1.1 (C)
unnamed: C37.2, R12.1
unnamed: C38.2, R8.1
unnamed: C39.2, R9.1
unnamed: C40.1, RV1.2
unnamed: C40.2, R10.1
unnamed: C41.2, R11.1
unnamed: C60.2, R45.1
unnamed: JP7.1 (A), R44.1, U19.15 (IOA6)
unnamed: Q1.2 (B), R7.2
unnamed: Q1.3 (E), R13.1, U19.3 (A), U19.4 (B), U19.38 (C)
unnamed: U12.1, U19.27 (BDIR)
unnamed: U12.4, U19.29 (BC1)
PSG_Mute: R7.1
SOUNDIN1: C38.1
SOUNDIN2: C39.1
TANGOUT: C60.1
~RESET: U19.23 (~RESET)
~WR: U12.2
