leomanes/stargate/kicad/version v2.1.3 production/ram_rom.kicad_sch

## KiCad design kicad/version v2.1.3 production/ram_rom.kicad_sch (2026-06-13)

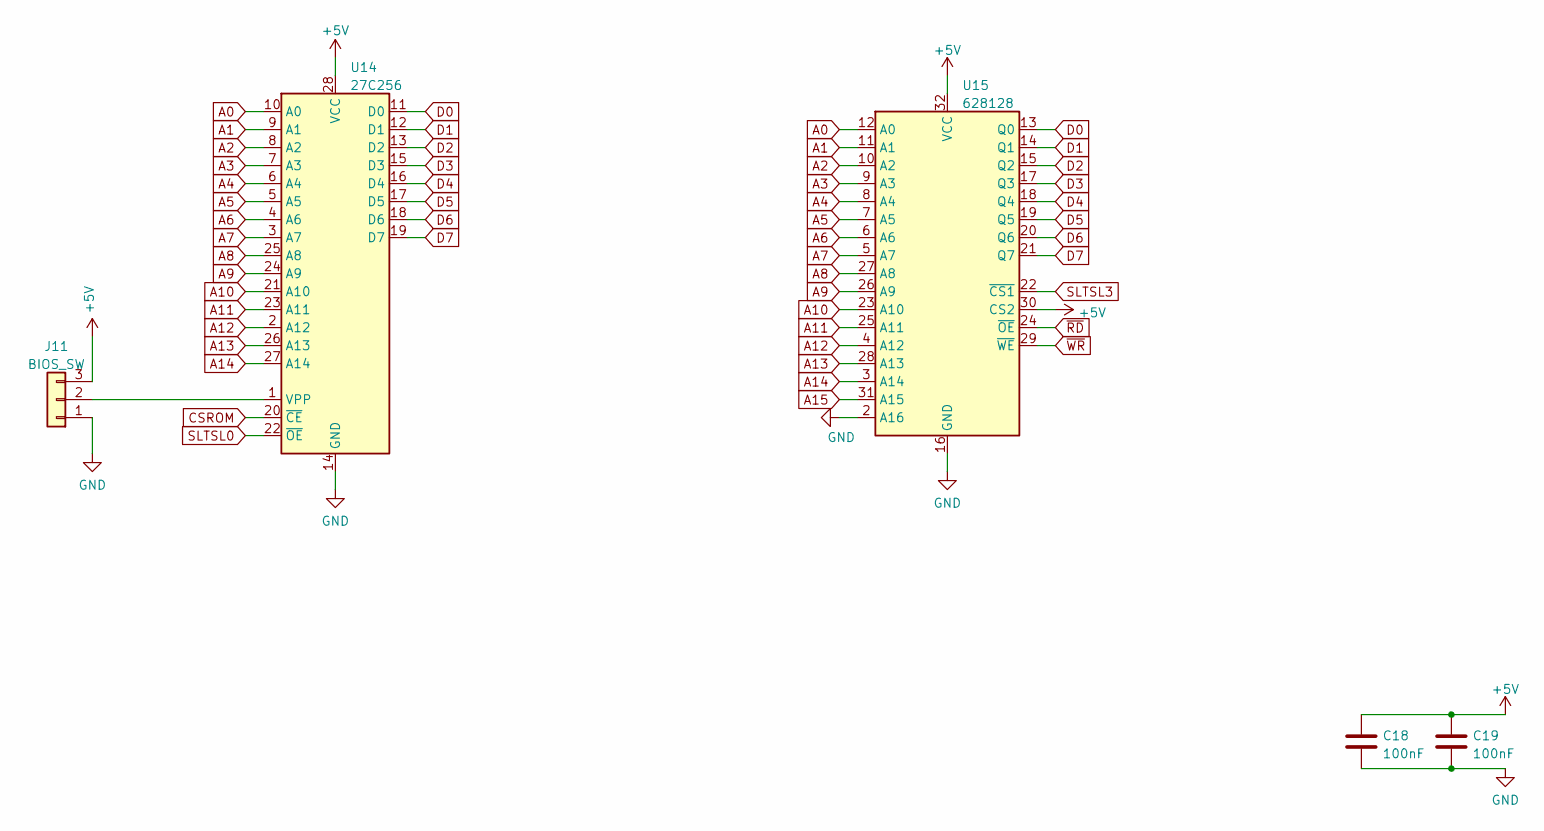
[picture p55: schematic ram_rom.kicad_sch]

Parts:
C18, C19: 100nF; C_Disc_D3.0mm_W2.0mm_P2.50mm
J11: BIOS_SW; PinHeader_1x03_P2.54mm_Vertical
U14: 27C256; DIP-28_W15.24mm_Socket
U15: 628128; DIP-32_W15.24mm_Socket

Connections:
+5V: C18.1, C19.1, J11.3, U14.28 (VCC), U15.30 (CS2), U15.32 (VCC)
A0: U14.10 (A0), U15.12 (A0)
A1: U14.9 (A1), U15.11 (A1)
A2: U14.8 (A2), U15.10 (A2)
A3: U14.7 (A3), U15.9 (A3)
A4: U14.6 (A4), U15.8 (A4)
A5: U14.5 (A5), U15.7 (A5)
A6: U14.4 (A6), U15.6 (A6)
A7: U14.3 (A7), U15.5 (A7)
A8: U14.25 (A8), U15.27 (A8)
A9: U14.24 (A9), U15.26 (A9)
A10: U14.21 (A10), U15.23 (A10)
A11: U14.23 (A11), U15.25 (A11)
A12: U14.2 (A12), U15.4 (A12)
A13: U14.26 (A13), U15.28 (A13)
A14: U14.27 (A14), U15.3 (A14)
A15: U15.31 (A15)
CSROM: U14.20 (~CE)
D0: U14.11 (D0), U15.13 (Q0)
D1: U14.12 (D1), U15.14 (Q1)
D2: U14.13 (D2), U15.15 (Q2)
D3: U14.15 (D3), U15.17 (Q3)
D4: U14.16 (D4), U15.18 (Q4)
D5: U14.17 (D5), U15.19 (Q5)
D6: U14.18 (D6), U15.20 (Q6)
D7: U14.19 (D7), U15.21 (Q7)
GND: C18.2, C19.2, J11.1, U14.14 (GND), U15.2 (A16), U15.16 (GND)
unnamed: J11.2, U14.1 (VPP)
SLTSL0: U14.22 (~OE)
SLTSL3: U15.22 (~CS1)
~RD: U15.24 (~OE)
~WR: U15.29 (~WE)
