leomanes/stargate/kicad/version v2.1.3 production/slots.kicad_sch

## KiCad design kicad/version v2.1.3 production/slots.kicad_sch (2026-06-13)

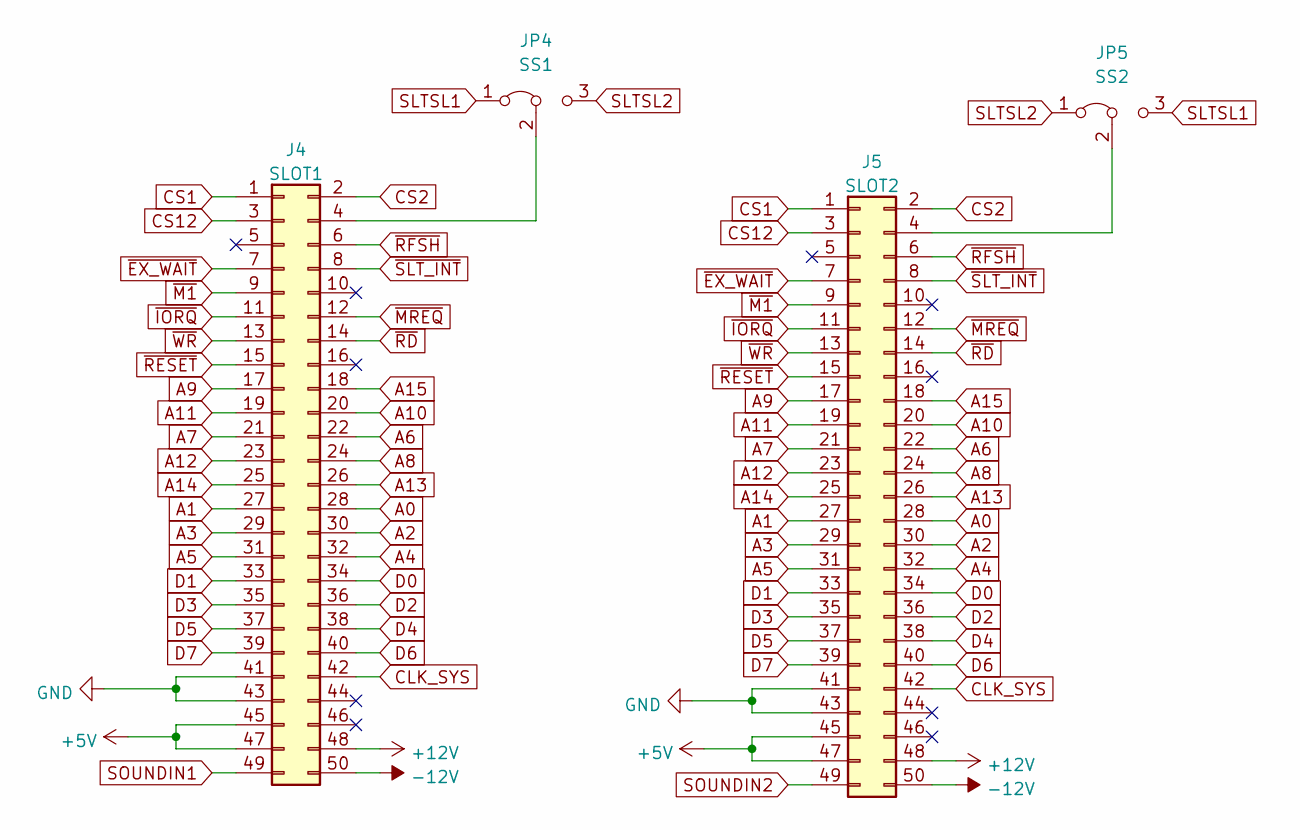
[picture p56: schematic slots.kicad_sch]

Parts:
J4: SLOT1; Conn_Edge_50P
J5: SLOT2; Conn_Edge_50P
JP4: SS1; SolderJumper-3_P1.3mm_Bridged12_Pad1.0x1.5mm_NumberLabels
JP5: SS2; SolderJumper-3_P1.3mm_Bridged12_Pad1.0x1.5mm_NumberLabels

Connections:
+5V: J4.45, J4.47, J5.45, J5.47
+12V: J4.48, J5.48
-12V: J4.50, J5.50
A0: J4.28, J5.28
A1: J4.27, J5.27
A2: J4.30, J5.30
A3: J4.29, J5.29
A4: J4.32, J5.32
A5: J4.31, J5.31
A6: J4.22, J5.22
A7: J4.21, J5.21
A8: J4.24, J5.24
A9: J4.17, J5.17
A10: J4.20, J5.20
A11: J4.19, J5.19
A12: J4.23, J5.23
A13: J4.26, J5.26
A14: J4.25, J5.25
A15: J4.18, J5.18
CLK_SYS: J4.42, J5.42
CS1: J4.1, J5.1
CS2: J4.2, J5.2
CS12: J4.3, J5.3
D0: J4.34, J5.34
D1: J4.33, J5.33
D2: J4.36, J5.36
D3: J4.35, J5.35
D4: J4.38, J5.38
D5: J4.37, J5.37
D6: J4.40, J5.40
D7: J4.39, J5.39
GND: J4.41, J4.43, J5.41, J5.43
unnamed: J4.4, JP4.2 (C)
unnamed: J5.4, JP5.2 (C)
SLTSL1: JP4.1 (A), JP5.3 (B)
SLTSL2: JP4.3 (B), JP5.1 (A)
SOUNDIN1: J4.49
SOUNDIN2: J5.49
~EX_WAIT: J4.7, J5.7
~IORQ: J4.11, J5.11
~M1: J4.9, J5.9
~MREQ: J4.12, J5.12
~RD: J4.14, J5.14
~RESET: J4.15, J5.15
~RFSH: J4.6, J5.6
~SLT_INT: J4.8, J5.8
~WR: J4.13, J5.13
