leomanes/stargate/kicad/version v2.1.3 production/video.kicad_sch

## KiCad design kicad/version v2.1.3 production/video.kicad_sch (2026-06-13)

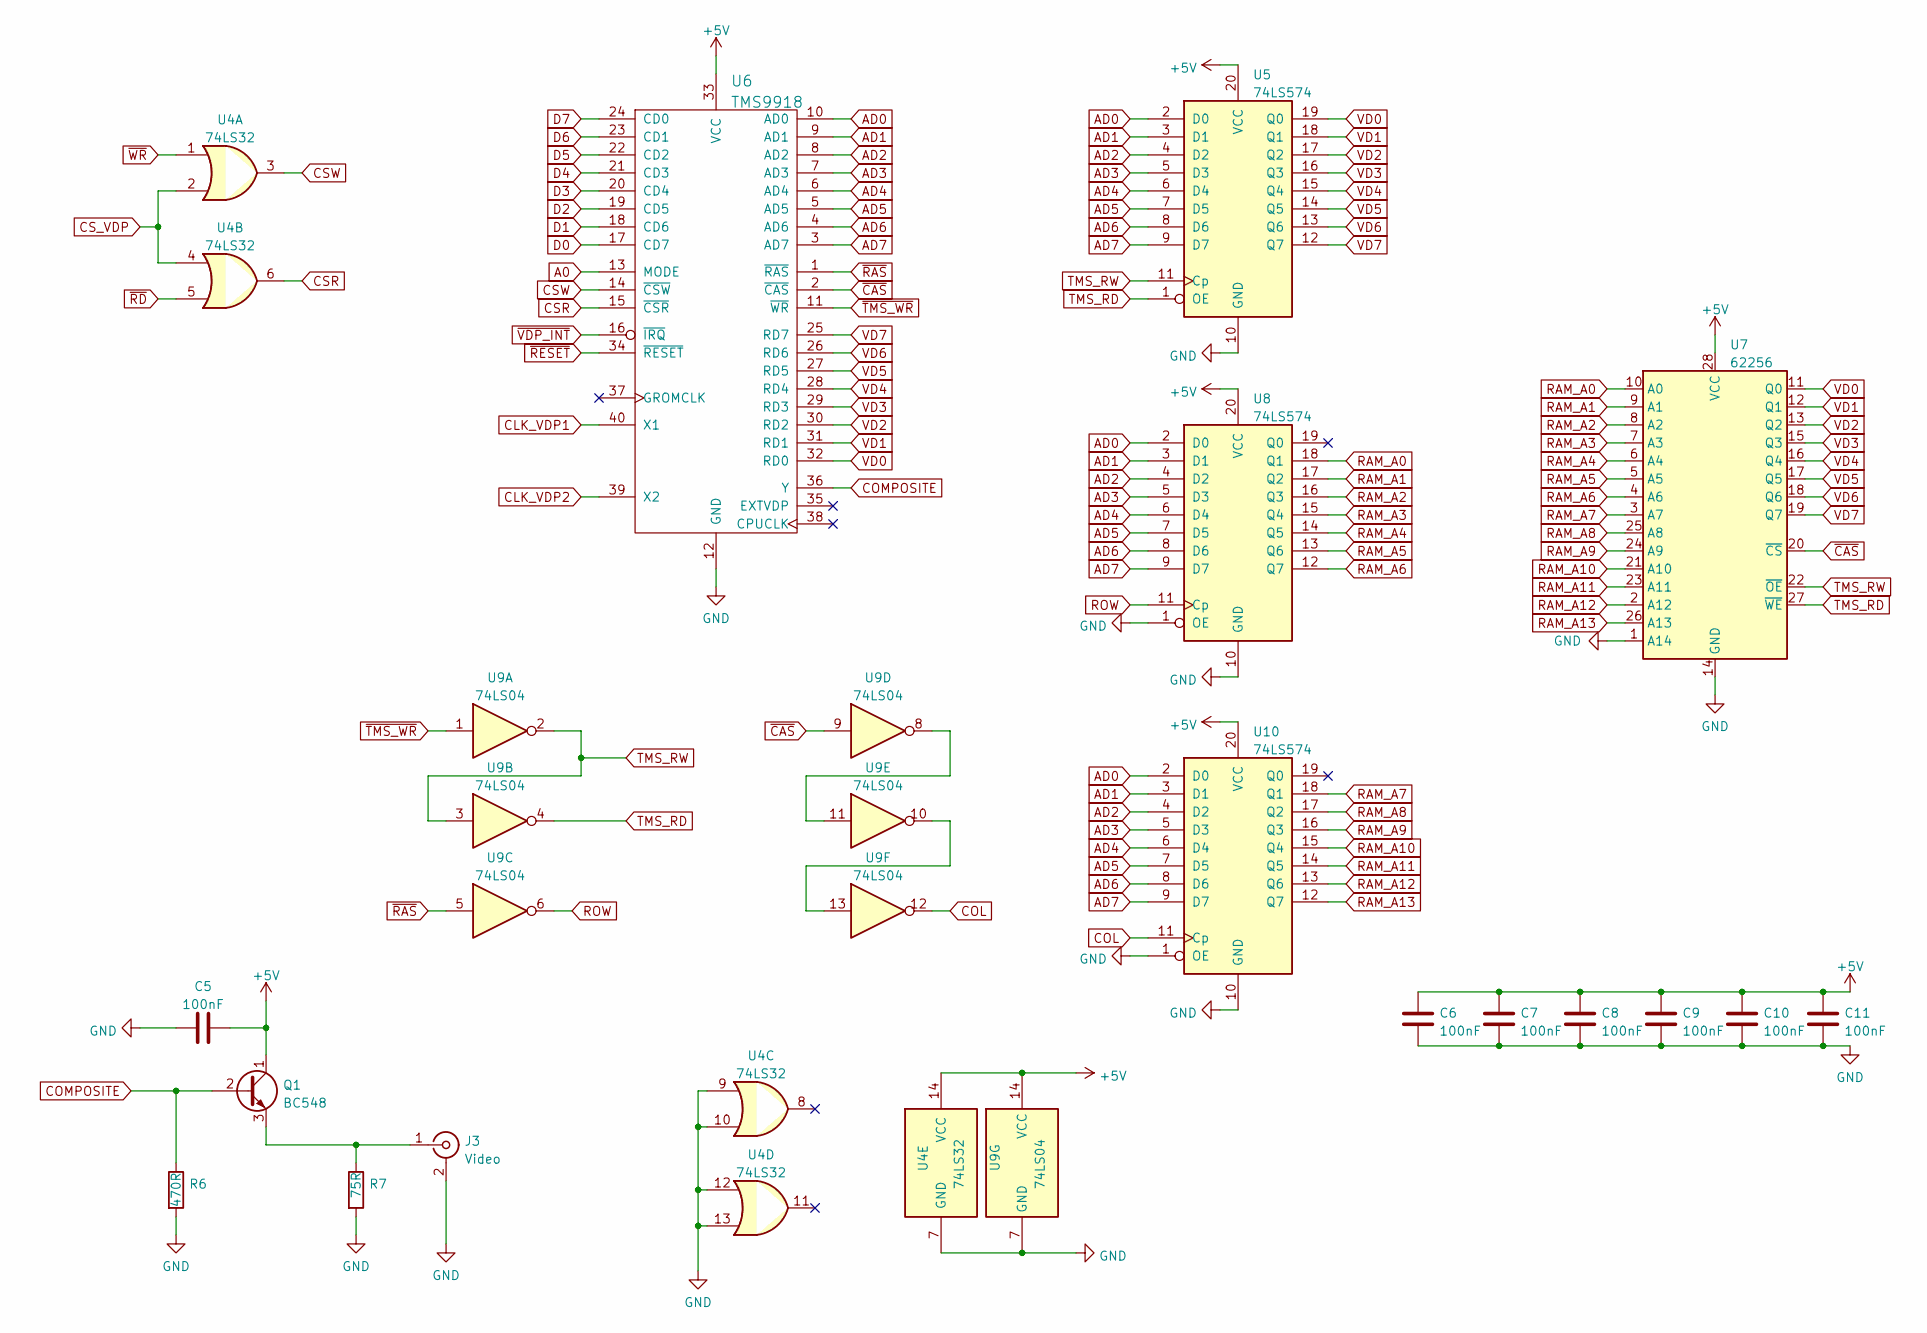
[picture p57: schematic video.kicad_sch]

Parts:
C5, C6, C7, C8, C9, C10, C11: 100nF; C_Disc_D3.0mm_W2.0mm_P2.50mm
J3: Video; Conn_RCA_Right
Q1: BC548; TO-92_Inline
R6: 470R; R_Axial_DIN0204_L3.6mm_D1.6mm_P7.62mm_Horizontal
R7: 75R; R_Axial_DIN0204_L3.6mm_D1.6mm_P7.62mm_Horizontal
U4: 74LS32; DIP-14_W7.62mm_Socket
U5, U8, U10: 74LS574; DIP-20_W7.62mm_Socket
U6: TMS9918; DIP-40_W15.24mm_Socket
U7: 62256; DIP-28_W15.24mm_Socket
U9: 74LS04; DIP-14_W7.62mm_Socket

Connections:
+5V: C5.2, C6.1, C7.1, C8.1, C9.1, C10.1, C11.1, Q1.1 (C), U4.14 (VCC), U5.20 (VCC), U6.33 (VCC), U7.28 (VCC), U8.20 (VCC), U9.14 (VCC), U10.20 (VCC)
A0: U6.13 (MODE)
AD0: U5.2 (D0), U6.10 (AD0), U8.2 (D0), U10.2 (D0)
AD1: U5.3 (D1), U6.9 (AD1), U8.3 (D1), U10.3 (D1)
AD2: U5.4 (D2), U6.8 (AD2), U8.4 (D2), U10.4 (D2)
AD3: U5.5 (D3), U6.7 (AD3), U8.5 (D3), U10.5 (D3)
AD4: U5.6 (D4), U6.6 (AD4), U8.6 (D4), U10.6 (D4)
AD5: U5.7 (D5), U6.5 (AD5), U8.7 (D5), U10.7 (D5)
AD6: U5.8 (D6), U6.4 (AD6), U8.8 (D6), U10.8 (D6)
AD7: U5.9 (D7), U6.3 (AD7), U8.9 (D7), U10.9 (D7)
CLK_VDP1: U6.40 (X1)
CLK_VDP2: U6.39 (X2)
COL: U9.12, U10.11 (Cp)
COMPOSITE: Q1.2 (B), R6.1, U6.36 (Y)
CSR: U4.6, U6.15 (~CSR)
CSW: U4.3, U6.14 (~CSW)
CS_VDP: U4.2, U4.4
D0: U6.17 (CD7)
D1: U6.18 (CD6)
D2: U6.19 (CD5)
D3: U6.20 (CD4)
D4: U6.21 (CD3)
D5: U6.22 (CD2)
D6: U6.23 (CD1)
D7: U6.24 (CD0)
GND: C5.1, C6.2, C7.2, C8.2, C9.2, C10.2, C11.2, J3.2 (Ext), R6.2, R7.2, U4.7 (GND), U4.9, U4.10, U4.12, U4.13, U5.10 (GND), U6.12 (GND), U7.1 (A14), U7.14 (GND), U8.1 (OE), U8.10 (GND), U9.7 (GND), U10.1 (OE), U10.10 (GND)
unnamed: J3.1 (In), Q1.3 (E), R7.1
unnamed: U9.10, U9.13
unnamed: U9.8, U9.11
RAM_A0: U7.10 (A0), U8.18 (Q1)
RAM_A1: U7.9 (A1), U8.17 (Q2)
RAM_A2: U7.8 (A2), U8.16 (Q3)
RAM_A3: U7.7 (A3), U8.15 (Q4)
RAM_A4: U7.6 (A4), U8.14 (Q5)
RAM_A5: U7.5 (A5), U8.13 (Q6)
RAM_A6: U7.4 (A6), U8.12 (Q7)
RAM_A7: U7.3 (A7), U10.18 (Q1)
RAM_A8: U7.25 (A8), U10.17 (Q2)
RAM_A9: U7.24 (A9), U10.16 (Q3)
RAM_A10: U7.21 (A10), U10.15 (Q4)
RAM_A11: U7.23 (A11), U10.14 (Q5)
RAM_A12: U7.2 (A12), U10.13 (Q6)
RAM_A13: U7.26 (A13), U10.12 (Q7)
ROW: U8.11 (Cp), U9.6
TMS_RD: U5.1 (OE), U7.27 (~WE), U9.4
TMS_RW: U5.11 (Cp), U7.22 (~OE), U9.2, U9.3
VD0: U5.19 (Q0), U6.32 (RD0), U7.11 (Q0)
VD1: U5.18 (Q1), U6.31 (RD1), U7.12 (Q1)
VD2: U5.17 (Q2), U6.30 (RD2), U7.13 (Q2)
VD3: U5.16 (Q3), U6.29 (RD3), U7.15 (Q3)
VD4: U5.15 (Q4), U6.28 (RD4), U7.16 (Q4)
VD5: U5.14 (Q5), U6.27 (RD5), U7.17 (Q5)
VD6: U5.13 (Q6), U6.26 (RD6), U7.18 (Q6)
VD7: U5.12 (Q7), U6.25 (RD7), U7.19 (Q7)
~CAS: U6.2 (~CAS), U7.20 (~CS), U9.9
~RAS: U6.1 (~RAS), U9.5
~RD: U4.5
~RESET: U6.34 (~RESET)
~TMS_WR: U6.11 (~WR), U9.1
~VDP_INT: U6.16 (~IRQ)
~WR: U4.1
