leomanes/stargate/kicad/version v2.1.3 production/wifi.kicad_sch

## KiCad design kicad/version v2.1.3 production/wifi.kicad_sch (2026-06-13)

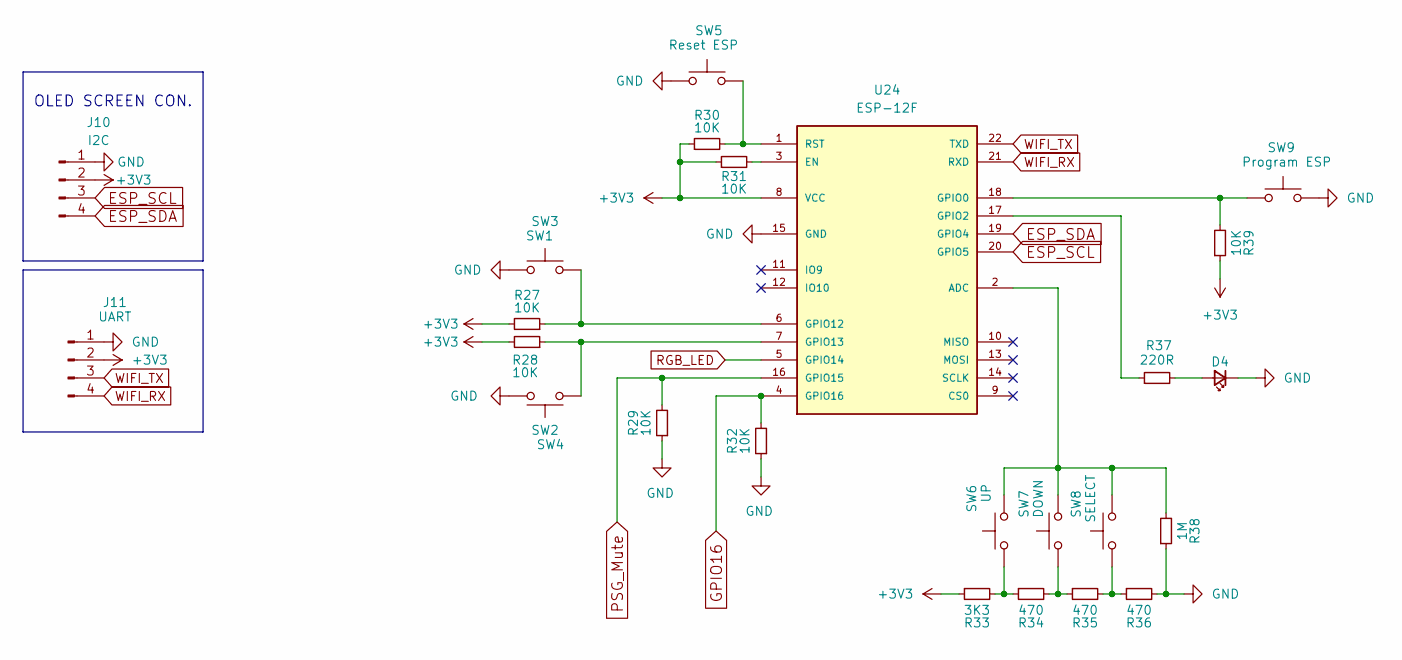
[picture p58: schematic wifi.kicad_sch]

Parts:
D4: WIFI_LED; LED_D3.0mm; LCSC C2290
J10: I2C; PinHeader_1x04_P2.54mm_Vertical
J11: UART; PinHeader_1x04_P2.54mm_Vertical
R27, R28, R29, R30, R31, R32, R39: 10K; R_Axial_DIN0204_L3.6mm_D1.6mm_P7.62mm_Horizontal; LCSC C11702
R33: 3K3; R_Axial_DIN0204_L3.6mm_D1.6mm_P7.62mm_Horizontal; LCSC C11702
R34, R35, R36: 470; R_Axial_DIN0204_L3.6mm_D1.6mm_P7.62mm_Horizontal; LCSC C11702
R37: 220R; R_Axial_DIN0204_L3.6mm_D1.6mm_P7.62mm_Horizontal; LCSC C11702
R38: 1M; R_Axial_DIN0204_L3.6mm_D1.6mm_P7.62mm_Horizontal; LCSC C11702
SW3: SW1; SW_Tactile_SPST_Angled_PTS645Vx83-2LFS
SW4: SW2; SW_Tactile_SPST_Angled_PTS645Vx83-2LFS
SW5: Reset ESP; SW_PUSH_6mm
SW6: UP; SW_PUSH_6mm
SW7: DOWN; SW_PUSH_6mm
SW8: SELECT; SW_PUSH_6mm
SW9: Program ESP; SW_PUSH_6mm
U24: ESP-12F

Connections:
+3V3: J10.2, J11.2, R27.2, R28.2, R30.1, R31.1, R33.1, R39.1, U24.8 (VCC)
ESP_SCL: J10.3, U24.20 (GPIO5)
ESP_SDA: J10.4, U24.19 (GPIO4)
GND: D4.1 (K), J10.1, J11.1, R29.1, R32.1, R36.2, R38.1, SW3.2, SW4.2, SW5.2, SW9.2, U24.15 (GND)
GPIO16: R32.2, U24.4 (GPIO16)
unnamed: D4.2 (A), R37.2
unnamed: R27.1, SW3.1, U24.6 (GPIO12)
unnamed: R28.1, SW4.1, U24.7 (GPIO13)
unnamed: R30.2, SW5.1, U24.1 (RST)
unnamed: R31.2, U24.3 (EN)
unnamed: R33.2, R34.1, SW6.1
unnamed: R34.2, R35.1, SW7.1
unnamed: R35.2, R36.1, SW8.1
unnamed: R37.1, U24.17 (GPIO2)
unnamed: R38.2, SW6.2, SW7.2, SW8.2, U24.2 (ADC)
unnamed: R39.2, SW9.1, U24.18 (GPIO0)
PSG_Mute: R29.2, U24.16 (GPIO15)
RGB_LED: U24.5 (GPIO14)
WIFI_RX: J11.4, U24.21 (RXD)
WIFI_TX: J11.3, U24.22 (TXD)

Notes on the sheet:
OLED SCREEN CON.
